PlusToolkit/PlusModelCatalog/fCalPhantom/fCal_1/PhantomDefinition_fCal_1.2_Wiring_1.1.png

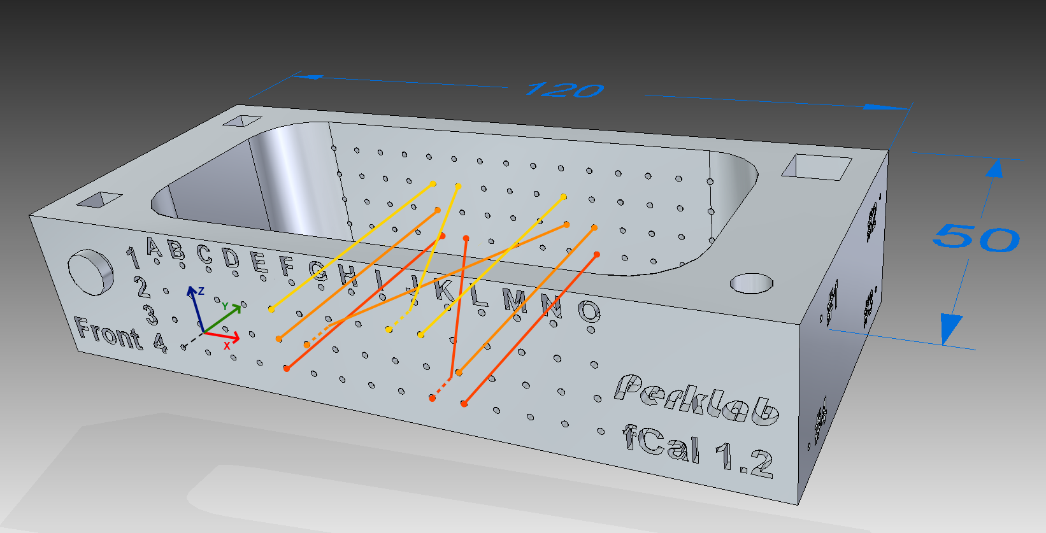
fCalPhantom/fCal_1/PhantomDefinition_fCal_1.2_Wiring_1.1.png
