PlusToolkit/PlusModelCatalog/fCalPhantom/fCal_3/fCal3.1-origin.png

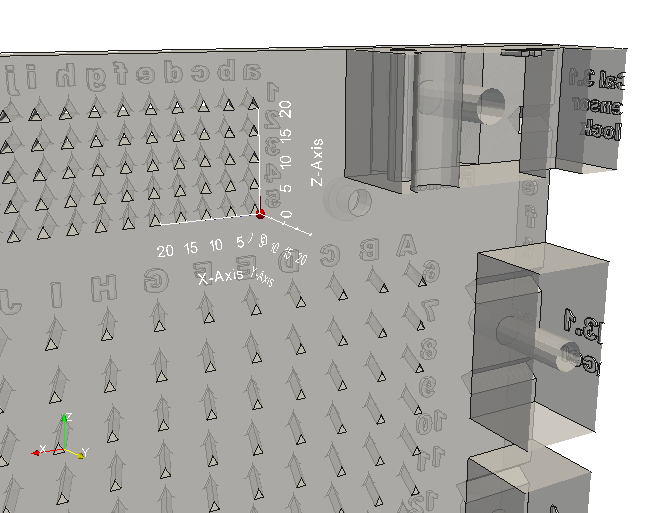
fCalPhantom/fCal_3/fCal3.1-origin.png
