PlusToolkit/PlusModelCatalog/fCalPhantom/fCal_3/fCal3.1.png

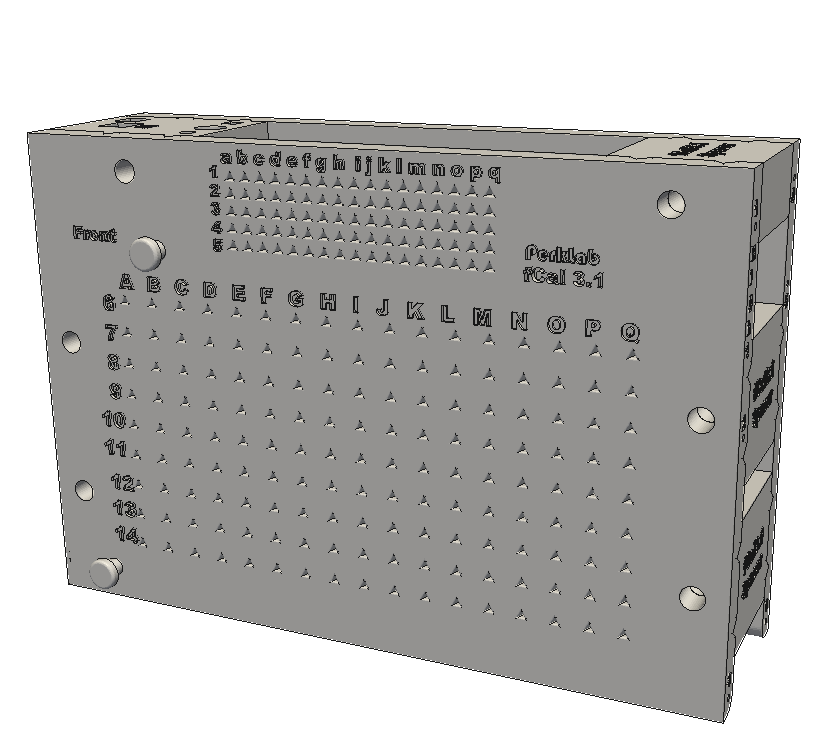
fCalPhantom/fCal_3/fCal3.1.png
