PlusToolkit/PlusModelCatalog/fCalPhantom/fCal_Echo/fCal_Echo1.0.png

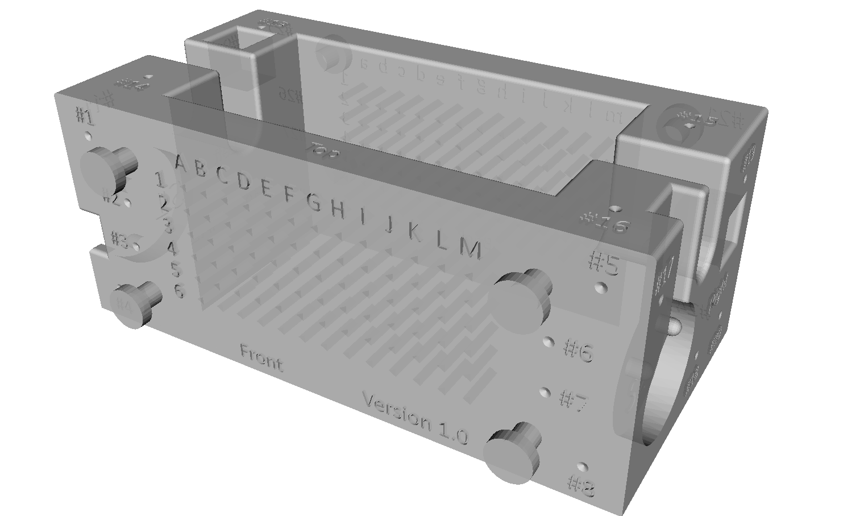
fCalPhantom/fCal_Echo/fCal_Echo1.0.png
