PlusToolkit/PlusModelCatalog/TrackingFixtures/Ascension800Holder_ThreeHolesUp.png

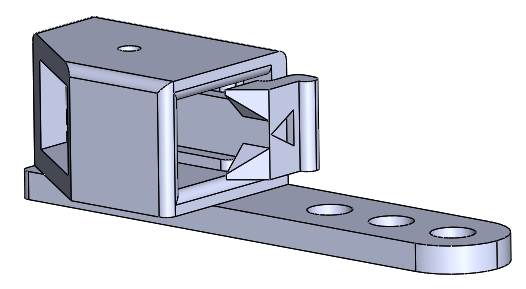
TrackingFixtures/Ascension800Holder_ThreeHolesUp.png
