PlusToolkit/PlusModelCatalog/TrackingFixtures/AscensionStyleAuroraHolder_1.0.PNG

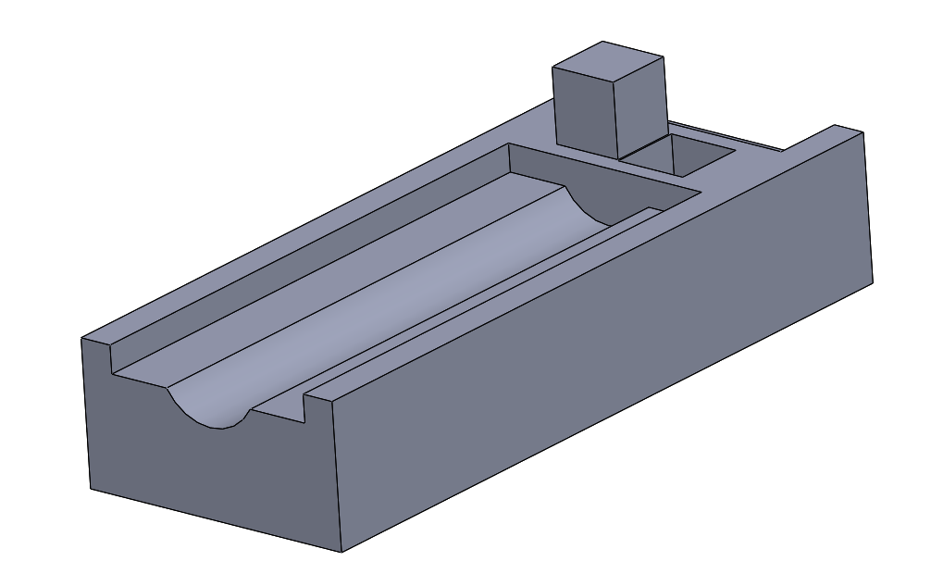
TrackingFixtures/AscensionStyleAuroraHolder_1.0.PNG
