PlusToolkit/PlusModelCatalog/TrackingFixtures/CandyCaneNeedleBase.PNG

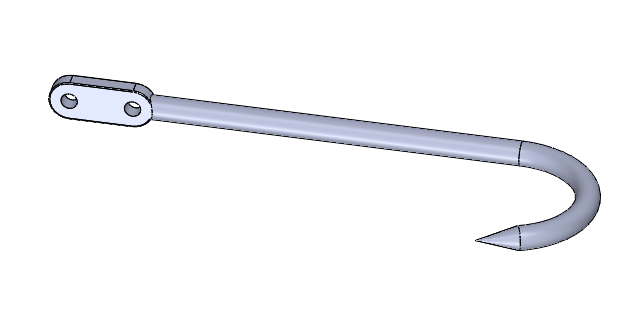
TrackingFixtures/CandyCaneNeedleBase.PNG
