PlusToolkit/PlusModelCatalog/TrackingFixtures/CandyCaneNeedleMarker.PNG

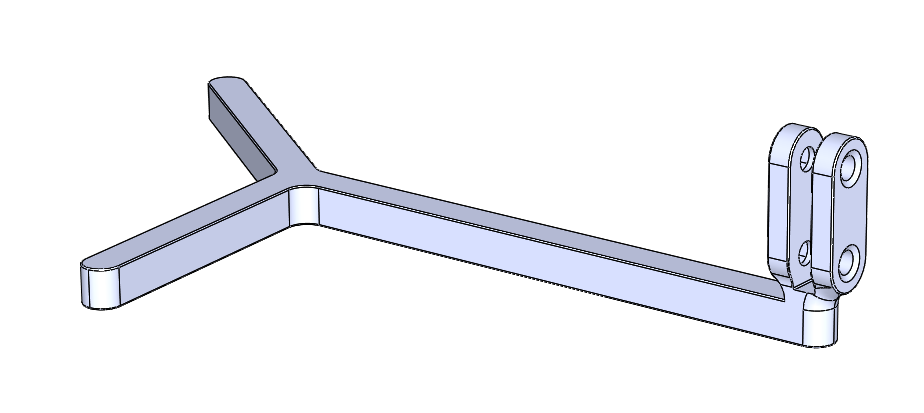
TrackingFixtures/CandyCaneNeedleMarker.PNG
