PlusToolkit/PlusModelCatalog/TrackingFixtures/CauteryGrabber.png

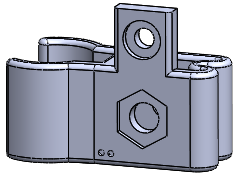
TrackingFixtures/CauteryGrabber.png
