PlusToolkit/PlusModelCatalog/TrackingFixtures/GE_ML6-15-D/GeMl615D_Clip_v01.png

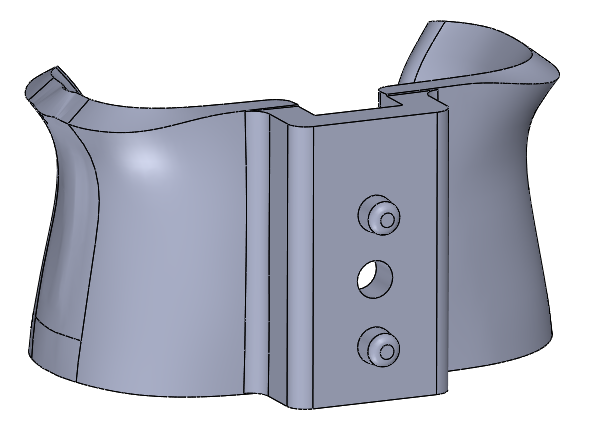
TrackingFixtures/GE_ML6-15-D/GeMl615D_Clip_v01.png
