PlusToolkit/PlusModelCatalog/TrackingFixtures/LureLockMale_SensorHolder.png

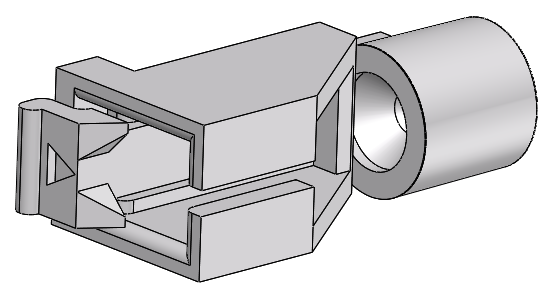
TrackingFixtures/LureLockMale_SensorHolder.png
