PlusToolkit/PlusModelCatalog/TrackingFixtures/NeedleGrabber-BardDuaLok.png

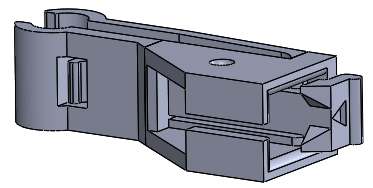
TrackingFixtures/NeedleGrabber-BardDuaLok.png
