PlusToolkit/PlusModelCatalog/TrackingFixtures/OrientationLR-Plane.png

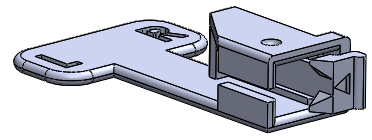
TrackingFixtures/OrientationLR-Plane.png
