PlusToolkit/PlusModelCatalog/TrackingFixtures/SensorHolder-OneHole.png

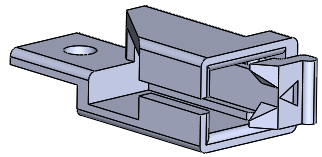
TrackingFixtures/SensorHolder-OneHole.png
