PlusToolkit/PlusModelCatalog/TrackingFixtures/Telemed-MicrUs-L12-SensorHolder.png

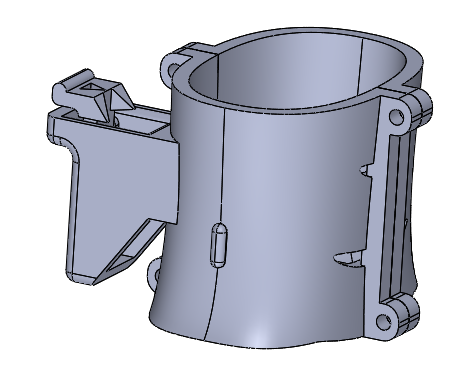
TrackingFixtures/Telemed-MicrUs-L12-SensorHolder.png
