PlusToolkit/PlusModelCatalog/TrackingFixtures/Telemed-MicruUs-C5/Telemed-C5-Brace.png

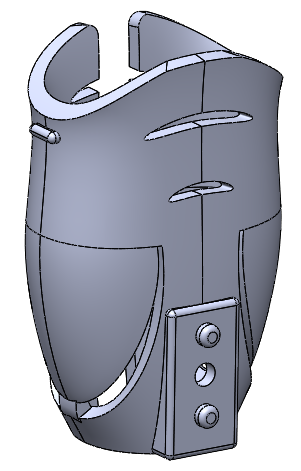
TrackingFixtures/Telemed-MicruUs-C5/Telemed-C5-Brace.png
