PlusToolkit/PlusModelCatalog/TrackingFixtures/Telemed-MicruUs-L12/Telemed-L12-ClipOn.png

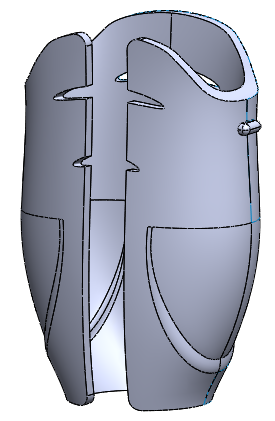
TrackingFixtures/Telemed-MicruUs-L12/Telemed-L12-ClipOn.png
