PlusToolkit/PlusModelCatalog/TrackingFixtures/TelemedHolder-L12_MarkedSide.png

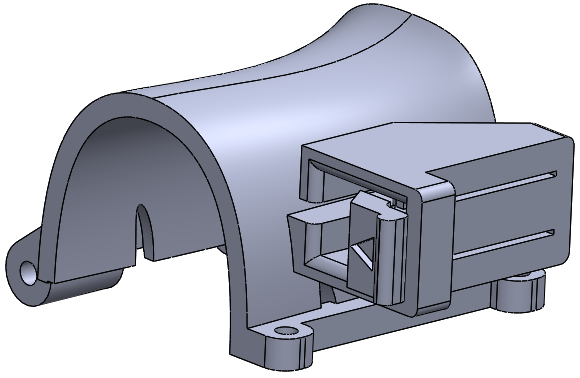
TrackingFixtures/TelemedHolder-L12_MarkedSide.png
