PlusToolkit/PlusModelCatalog/TrackingFixtures/TelemedHolder-L12_UnmarkedSide.png

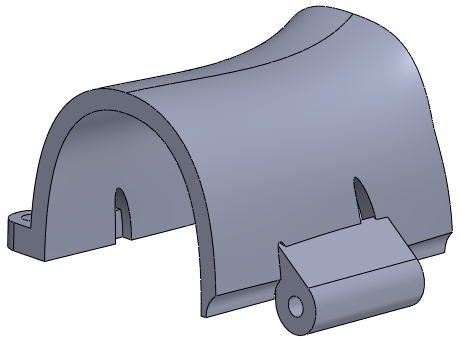
TrackingFixtures/TelemedHolder-L12_UnmarkedSide.png
