PlusToolkit/PlusModelCatalog/fCalPhantom/fCal_L1/BuildingInstructionManual/LPub/parts/3007_14_1275_150_DPCM_1_23_-45.png

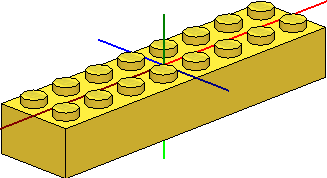
fCalPhantom/fCal_L1/BuildingInstructionManual/LPub/parts/3007_14_1275_150_DPCM_1_23_-45.png
