PlusToolkit/PlusModelCatalog/TrackingFixtures/MC10_ProbeHolder/TelemedMC10_ProbeHolder_MarkedSide.SLDPRT

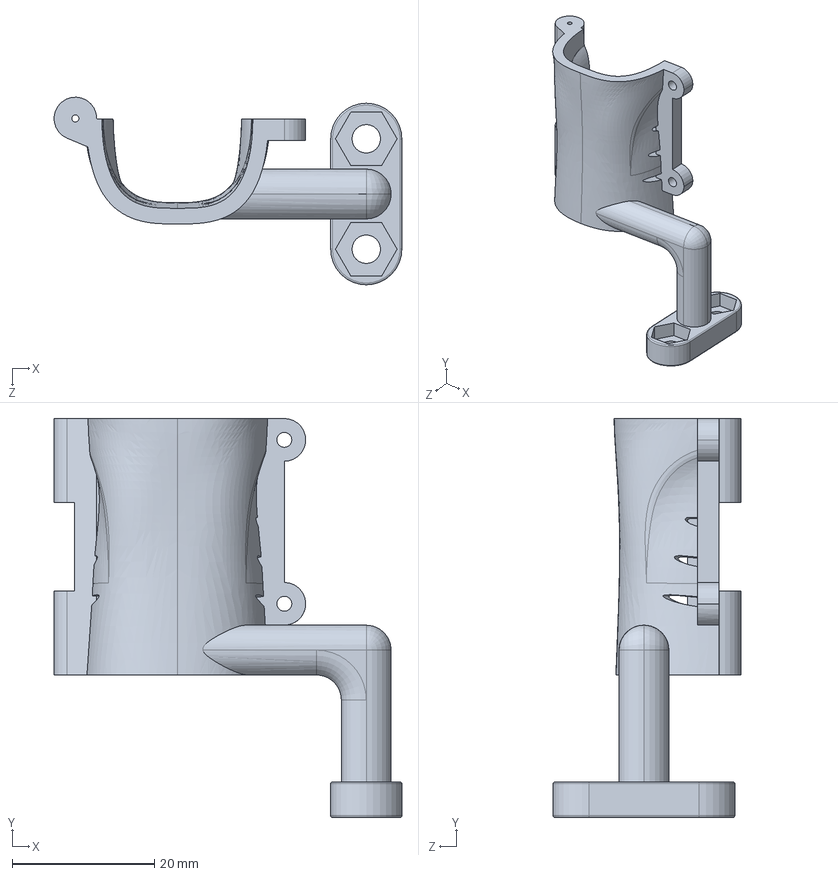
[picture p41: CAD file, 2016-08-29]
TrackingFixtures/MC10_ProbeHolder/TelemedMC10_ProbeHolder_MarkedSide.SLDPRT
48.8 x 56.0 x 26.3 mm
