PlusToolkit/PlusModelCatalog/TrackingFixtures/MicronTracker/MarkerHolder_120mm_Winged_1.0.stl

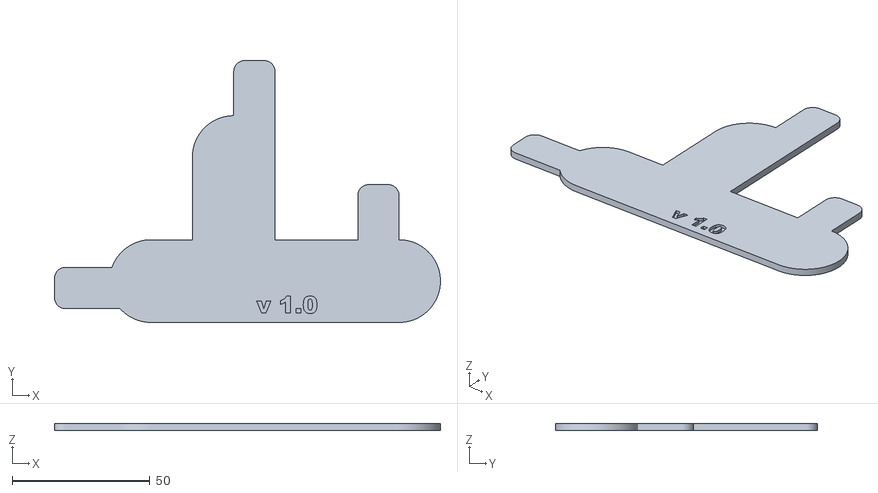
[picture p42: CAD file, 2014-11-28]
TrackingFixtures/MicronTracker/MarkerHolder_120mm_Winged_1.0.stl
140.0 x 95.0 x 2.50
