PlusToolkit/PlusModelCatalog/TrackingFixtures/MultiModalityTracking/SolidWorks/peg1.SLDPRT

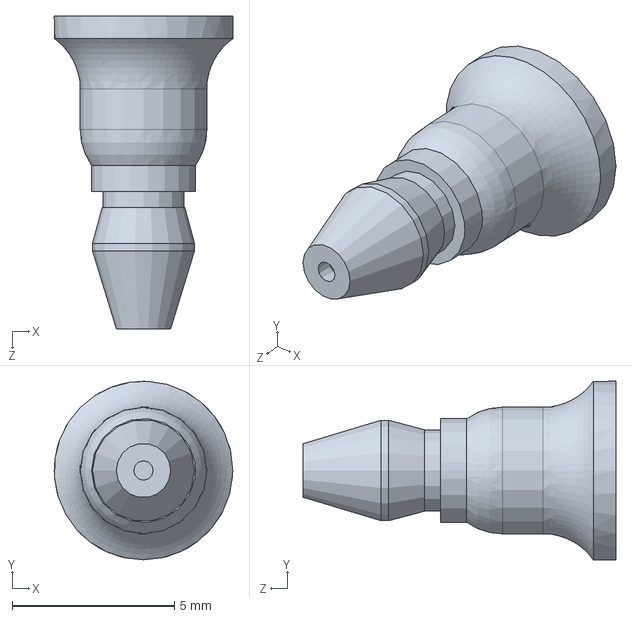
[picture p43: CAD file, 2017-01-05]
TrackingFixtures/MultiModalityTracking/SolidWorks/peg1.SLDPRT
5.50 x 5.50 x 9.64 mm
