PlusToolkit/PlusModelCatalog/TrackingFixtures/OpticalMarkerTracker/Marker-80.SLDPRT

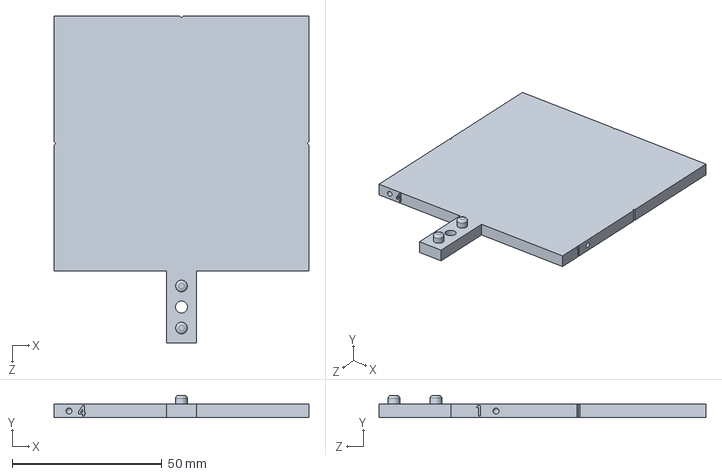
[picture p44: CAD file, 2017-06-23]
TrackingFixtures/OpticalMarkerTracker/Marker-80.SLDPRT
85.0 x 7.50 x 109.0 mm
