PlusToolkit/PlusModelCatalog/TrackingFixtures/OptiTrack/Marker_Ultrasound-OptiTrack.SLDPRT

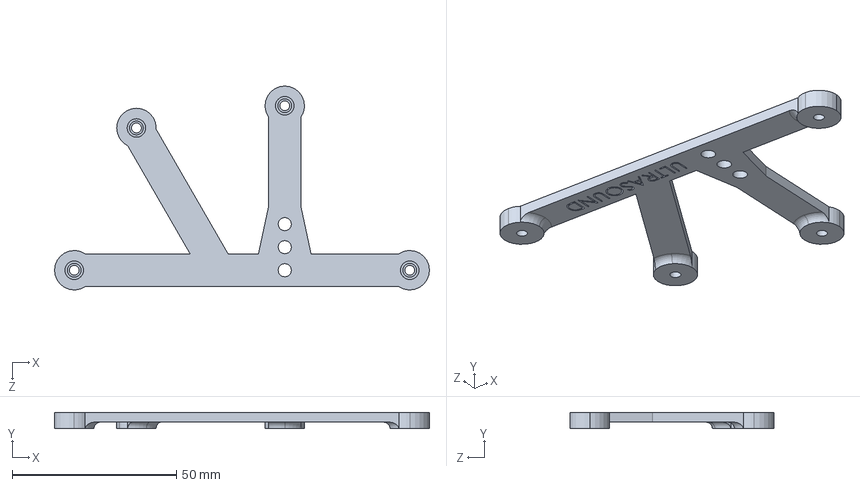
[picture p45: CAD file, 2017-10-10]
TrackingFixtures/OptiTrack/Marker_Ultrasound-OptiTrack.SLDPRT
114.0 x 5.00 x 62.0 mm
