PlusToolkit/PlusModelCatalog/TrackingFixtures/StealthStation/StylusMarker2.SLDPRT

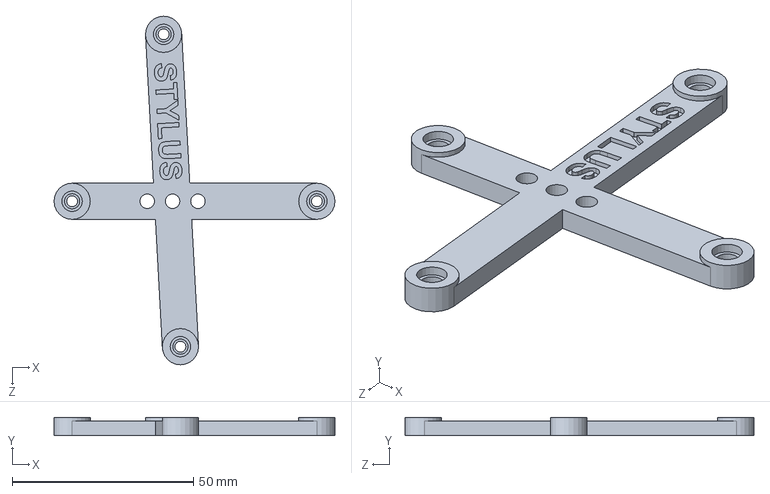
[picture p46: CAD file, 2018-01-19]
TrackingFixtures/StealthStation/StylusMarker2.SLDPRT
77.5 x 5.00 x 96.1 mm
