PlusToolkit/PlusModelCatalog/TrackingFixtures/Telemed-MicruUs-C5/Telemed-C5-Brace.SLDPRT

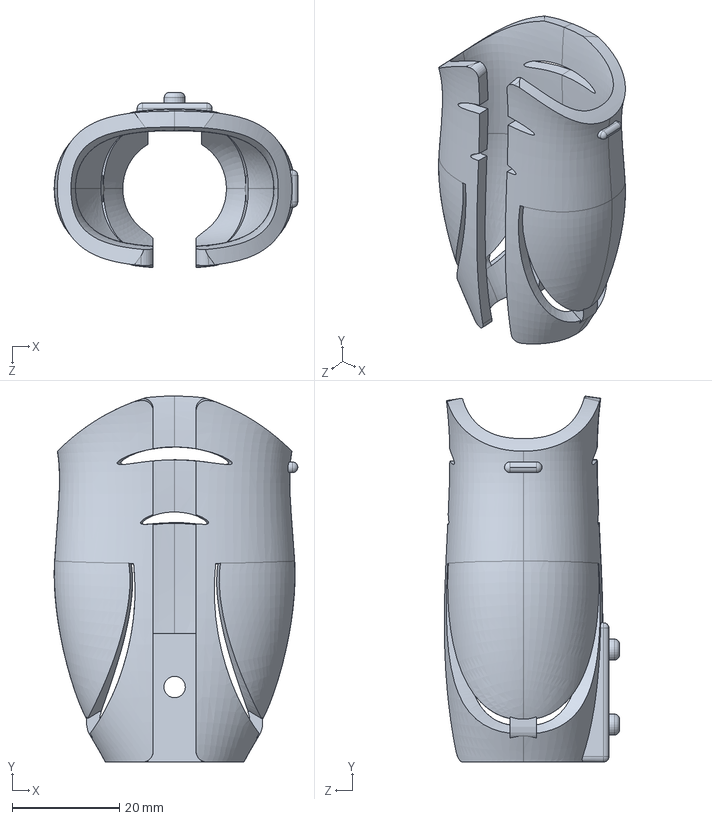
[picture p47: CAD file, 2017-04-27]
TrackingFixtures/Telemed-MicruUs-C5/Telemed-C5-Brace.SLDPRT
45.5 x 68.3 x 32.7 mm
