PlusToolkit/PlusModelCatalog/TrackingFixtures/Telemed-MicruUs-L12/Telemed-L12-ClipOn.SLDPRT

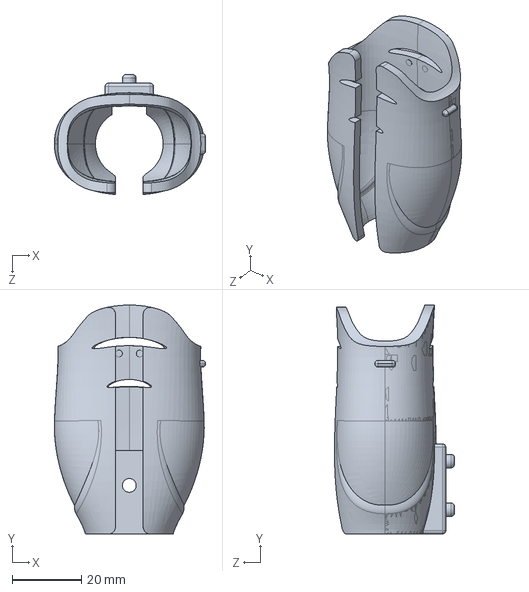
[picture p48: CAD file, 2017-05-24]
TrackingFixtures/Telemed-MicruUs-L12/Telemed-L12-ClipOn.SLDPRT
43.6 x 66.0 x 34.6 mm
