PlusToolkit/PlusModelCatalog/TrackingFixtures/UsCalibrationStylusMarker.stl

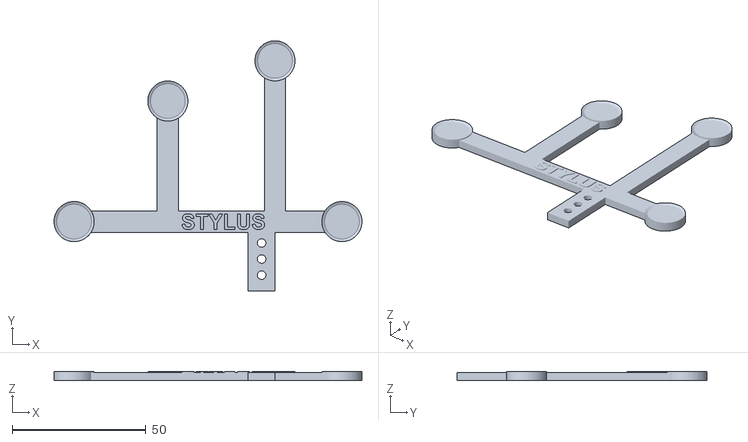
[picture p49: CAD file, 2018-02-23]
TrackingFixtures/UsCalibrationStylusMarker.stl
115.0 x 93.5 x 3.50
