PlusToolkit/PlusModelCatalog/UsNeedleTutor/PhantomFrame.SLDPRT

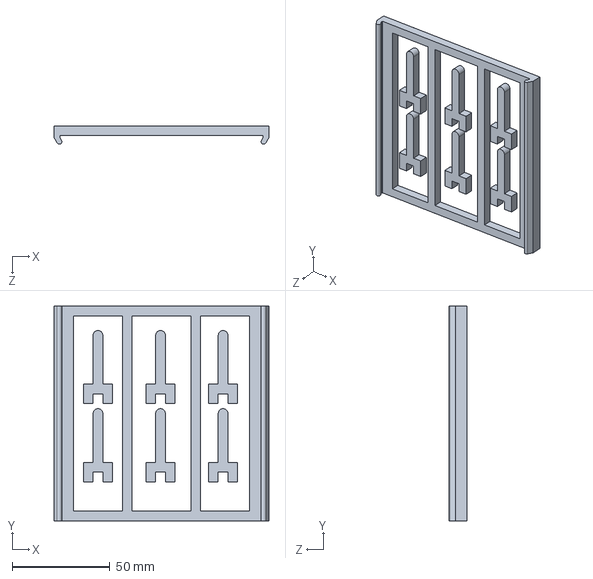
[picture p50: CAD file, 2018-01-30]
UsNeedleTutor/PhantomFrame.SLDPRT
110.0 x 110.0 x 9.45 mm
