PlusToolkit/PlusModelCatalog/fCalPhantom/fCal_3/fCal_3.1_left.stl

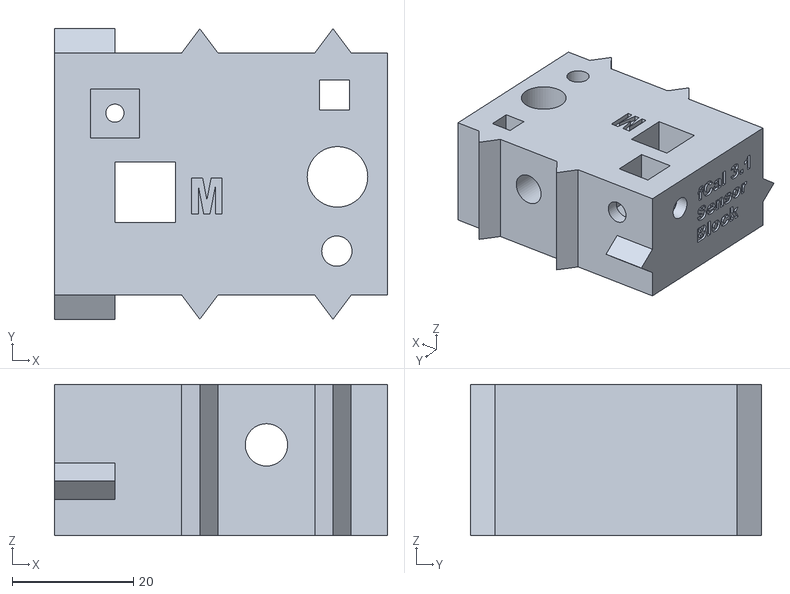
[picture p51: CAD file, 2014-11-28]
fCalPhantom/fCal_3/fCal_3.1_left.stl
55.0 x 48.0 x 25.0
