PlusToolkit/PlusModelCatalog/Tools/Needle_BardDuaLok57.stl

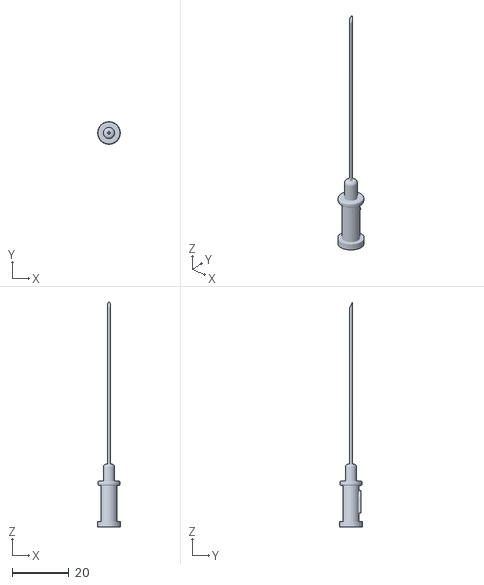
[picture p52: CAD file, 2016-08-08]
Tools/Needle_BardDuaLok57.stl
8.00 x 8.00 x 79.1
