PlusToolkit/PlusModelCatalog/TrackingFixtures/MicronTracker/MarkerHolder_120mm-even_short.stl

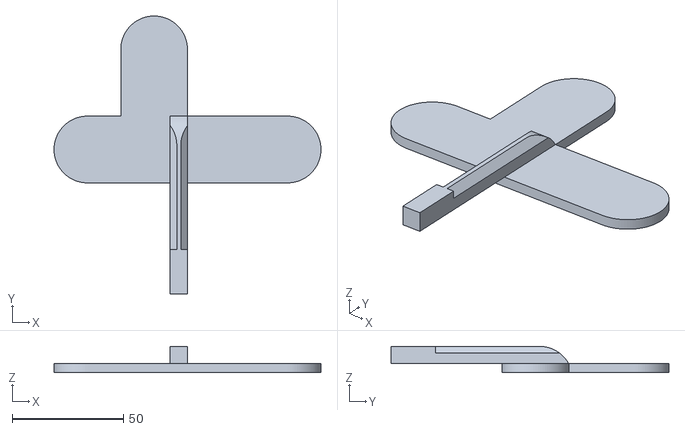
[picture p53: CAD file, 2014-11-28]
TrackingFixtures/MicronTracker/MarkerHolder_120mm-even_short.stl
120.0 x 124.9 x 11.8
