PlusToolkit/PlusModelCatalog/TrackingFixtures/MultiModalityTracking/SolidWorks/SensorHolder_1.0.SLDPRT

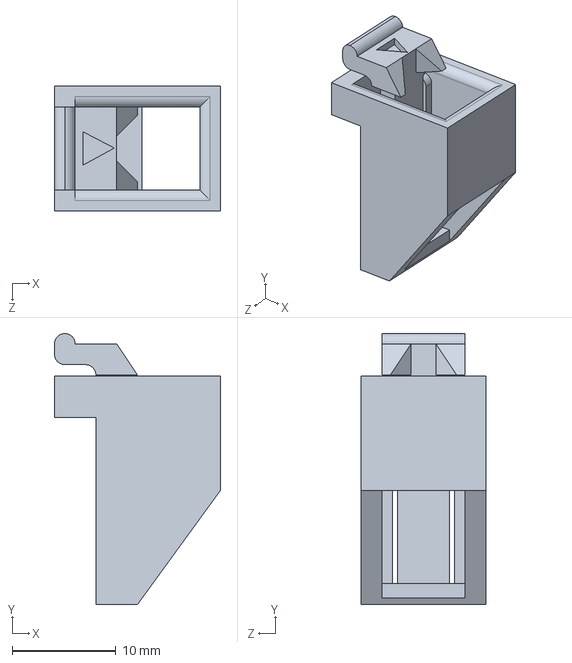
[picture p54: CAD file, 2017-01-05]
TrackingFixtures/MultiModalityTracking/SolidWorks/SensorHolder_1.0.SLDPRT
16.0 x 26.1 x 12.0 mm
