PlusToolkit/PlusModelCatalog/TrackingFixtures/OptiTrack/Marker_Stylus-OptiTrack.SLDPRT

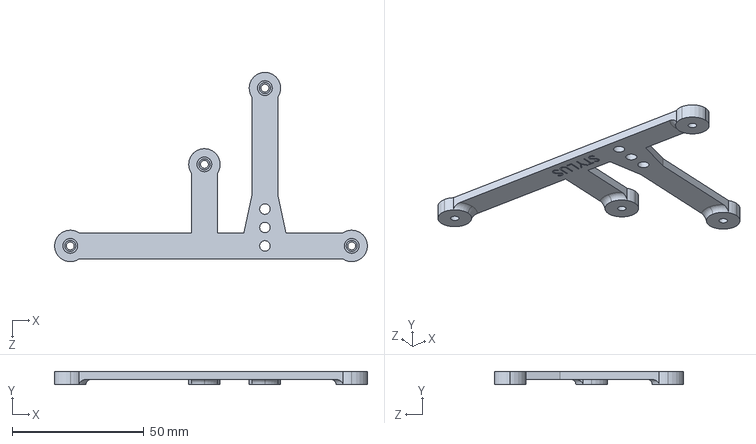
[picture p55: CAD file, 2017-10-10]
TrackingFixtures/OptiTrack/Marker_Stylus-OptiTrack.SLDPRT
119.0 x 5.00 x 72.0 mm
