PlusToolkit/PlusModelCatalog/TrackingFixtures/StealthStation/Stylus_Polaris.SLDPRT

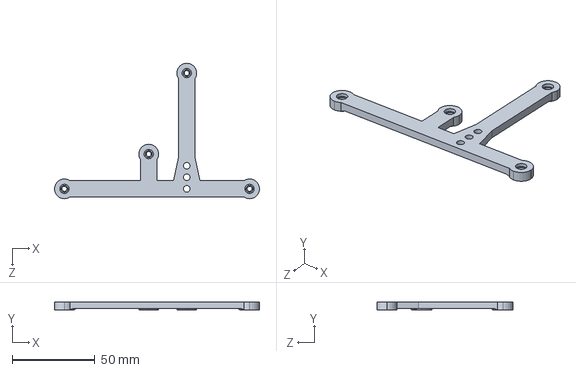
[picture p56: CAD file, 2017-11-28]
TrackingFixtures/StealthStation/Stylus_Polaris.SLDPRT
124.0 x 5.00 x 82.0 mm
