PlusToolkit/PlusModelCatalog/TrackingFixtures/Telemed-MicruUs-C5/Telemed-C5-2R60S.SLDPRT

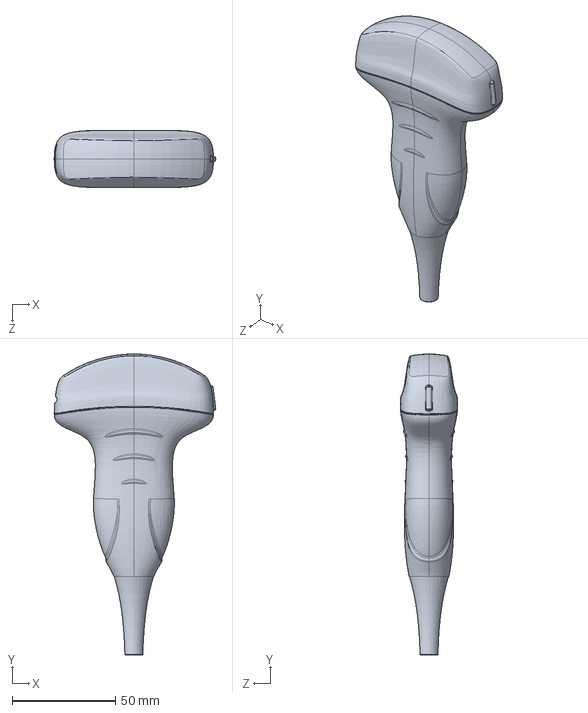
[picture p57: CAD file, 2017-04-27]
TrackingFixtures/Telemed-MicruUs-C5/Telemed-C5-2R60S.SLDPRT
78.1 x 145.5 x 27.7 mm
