PlusToolkit/PlusModelCatalog/TrackingFixtures/UsCalibrationStylus10cm.stl

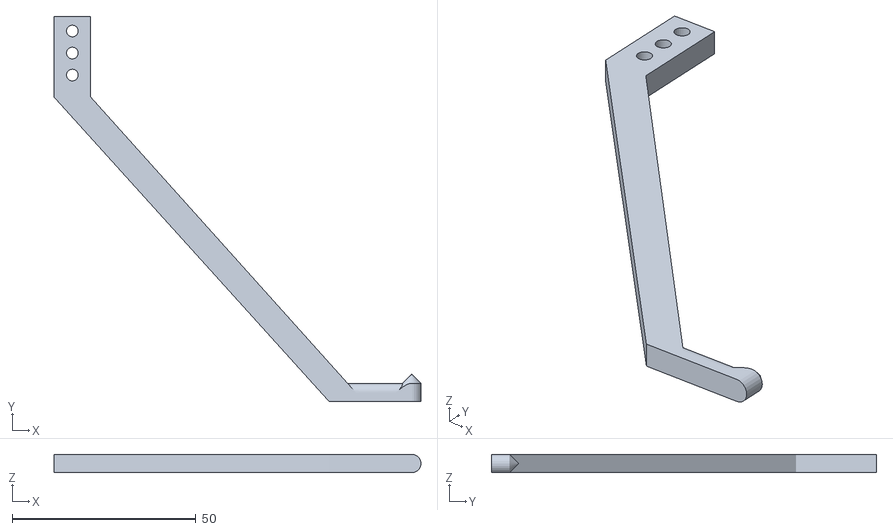
[picture p58: CAD file, 2018-02-23]
TrackingFixtures/UsCalibrationStylus10cm.stl
100.0 x 105.0 x 5.00
