PlusToolkit/PlusModelCatalog/UsNeedleTutor/NeedleMarker.SLDPRT

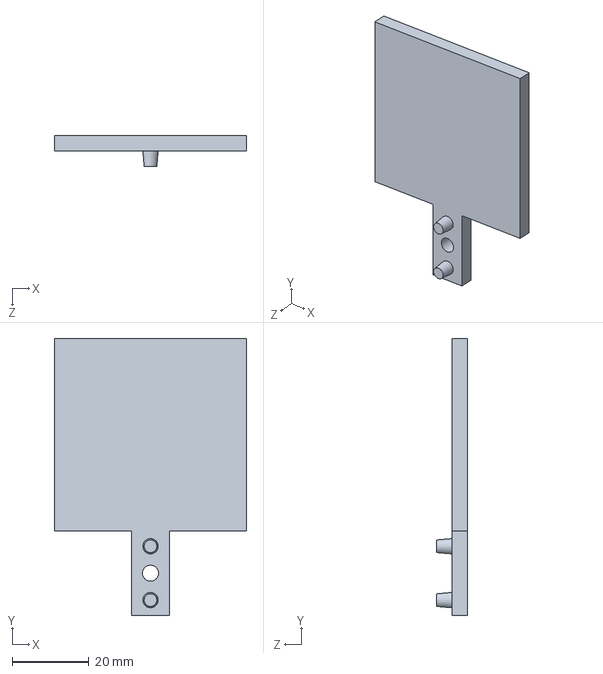
[picture p59: CAD file, 2018-01-30]
UsNeedleTutor/NeedleMarker.SLDPRT
50.0 x 72.0 x 8.00 mm
