PlusToolkit/PlusModelCatalog/fCalPhantom/fCal_3/fCal_3.1_front.stl

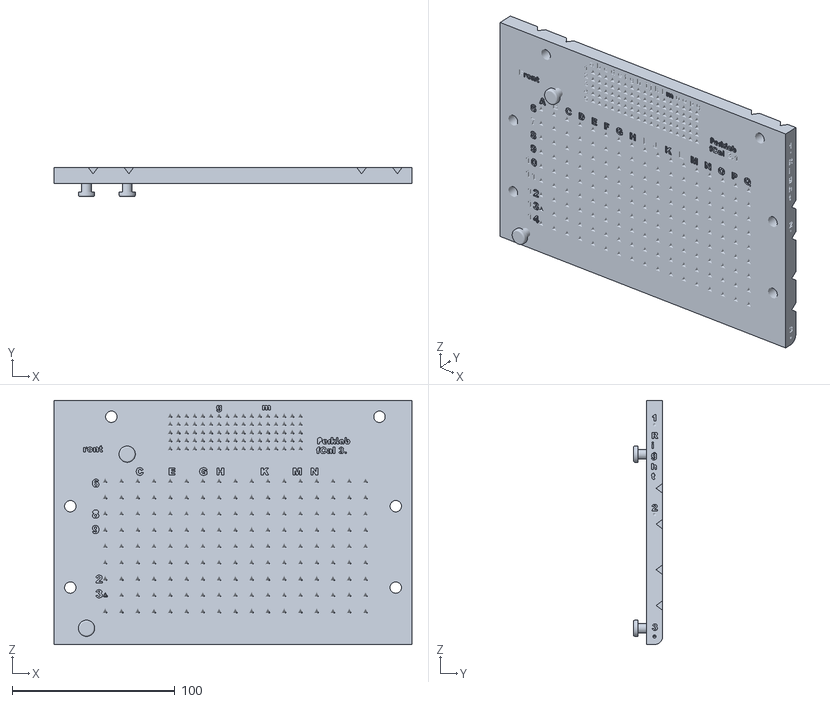
[picture p60: CAD file, 2014-11-28]
fCalPhantom/fCal_3/fCal_3.1_front.stl
220.0 x 18.0 x 150.0
