PlusToolkit/PlusModelCatalog/Tools/UsProbe_Telemed_L12.stl

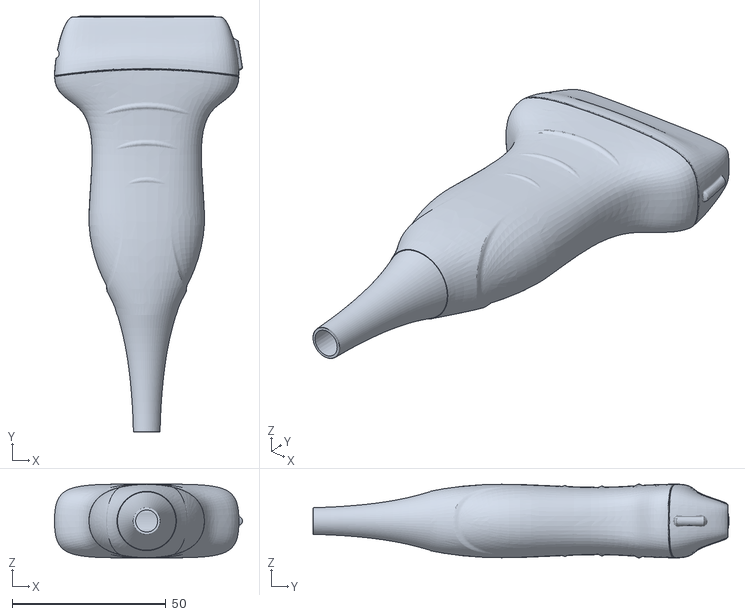
[picture p61: CAD file, 2016-08-08]
Tools/UsProbe_Telemed_L12.stl
61.2 x 135.3 x 24.1
