PlusToolkit/PlusModelCatalog/TrackingFixtures/Block4x4-ThreeHoles.SLDPRT

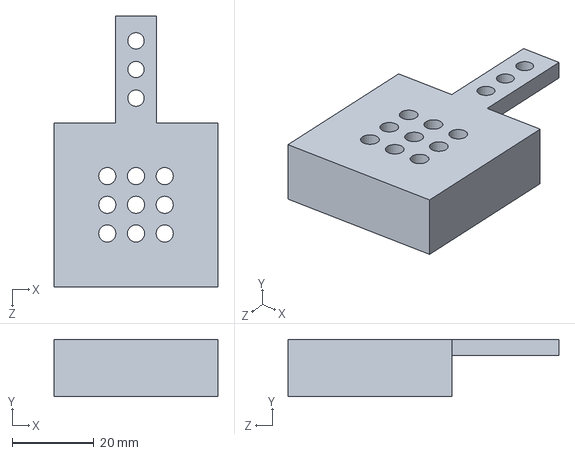
[picture p62: CAD file, 2017-11-28]
TrackingFixtures/Block4x4-ThreeHoles.SLDPRT
40.0 x 14.0 x 66.0 mm
