PlusToolkit/PlusModelCatalog/TrackingFixtures/MC10_ProbeHolder/TelemedMC10_ProbeHolder_UnmarkedSide.SLDPRT

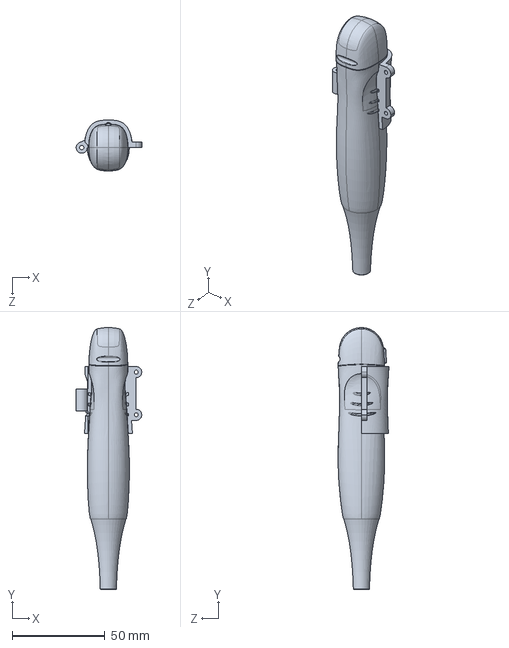
[picture p63: CAD file, 2016-08-05]
TrackingFixtures/MC10_ProbeHolder/TelemedMC10_ProbeHolder_UnmarkedSide.SLDPRT
35.3 x 141.0 x 27.3 mm
