PlusToolkit/PlusModelCatalog/TrackingFixtures/MicronTracker/MarkerHolder_120mm-Short_2.0.stl

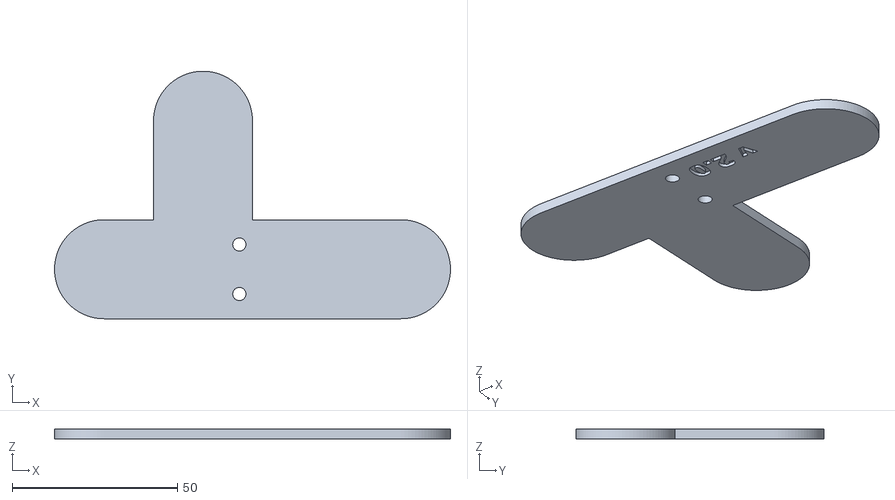
[picture p64: CAD file, 2014-11-28]
TrackingFixtures/MicronTracker/MarkerHolder_120mm-Short_2.0.stl
120.0 x 75.0 x 3.00
