PlusToolkit/PlusModelCatalog/TrackingFixtures/MultiModalityTracking/SolidWorks/PolarisAscensionPlane.SLDPRT

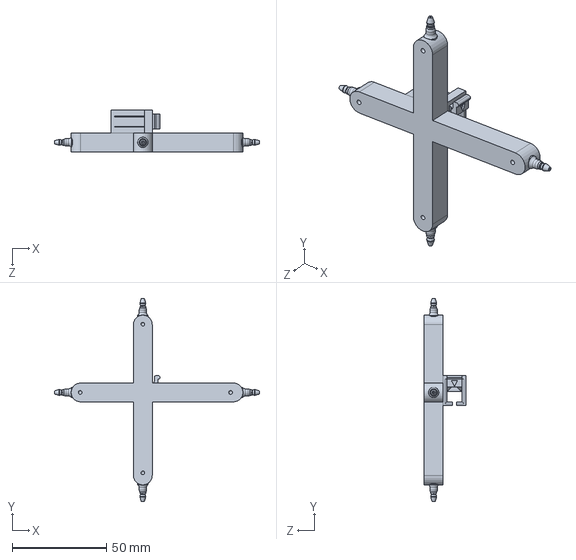
[picture p65: CAD file, 2017-01-05]
TrackingFixtures/MultiModalityTracking/SolidWorks/PolarisAscensionPlane.SLDPRT
108.6 x 107.6 x 22.0 mm
