PlusToolkit/PlusModelCatalog/TrackingFixtures/StealthStation/Ultrasound_Polaris.SLDPRT

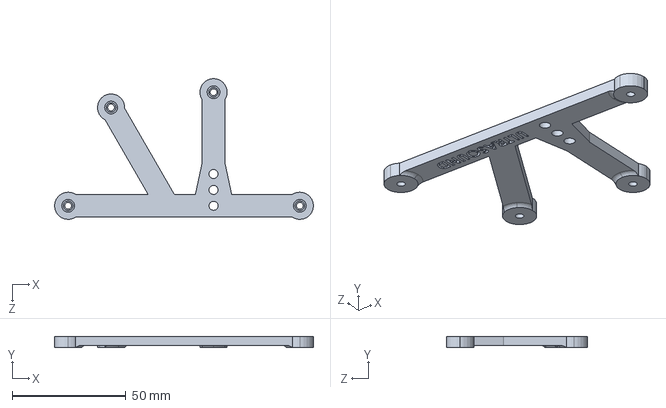
[picture p66: CAD file, 2017-11-28]
TrackingFixtures/StealthStation/Ultrasound_Polaris.SLDPRT
114.0 x 5.00 x 62.0 mm
