PlusToolkit/PlusModelCatalog/UsNeedleTutor/Reference.SLDPRT

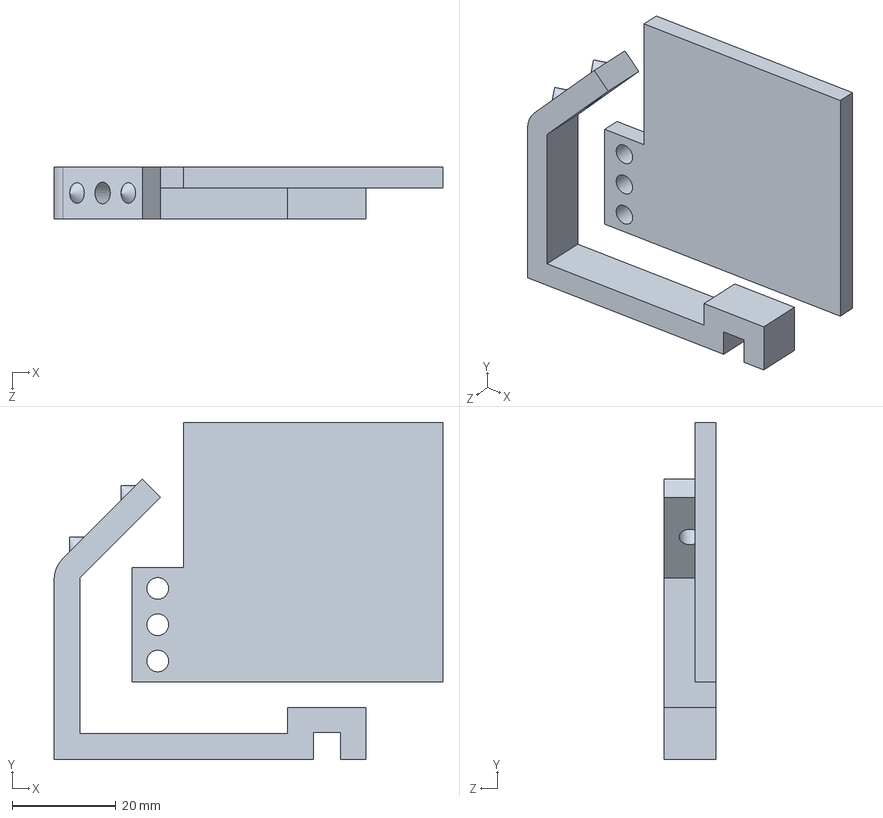
[picture p67: CAD file, 2018-01-30]
UsNeedleTutor/Reference.SLDPRT
75.0 x 65.0 x 10.0 mm
