PlusToolkit/PlusModelCatalog/fCalPhantom/fCal_3/fCal_3.1_spacer.stl

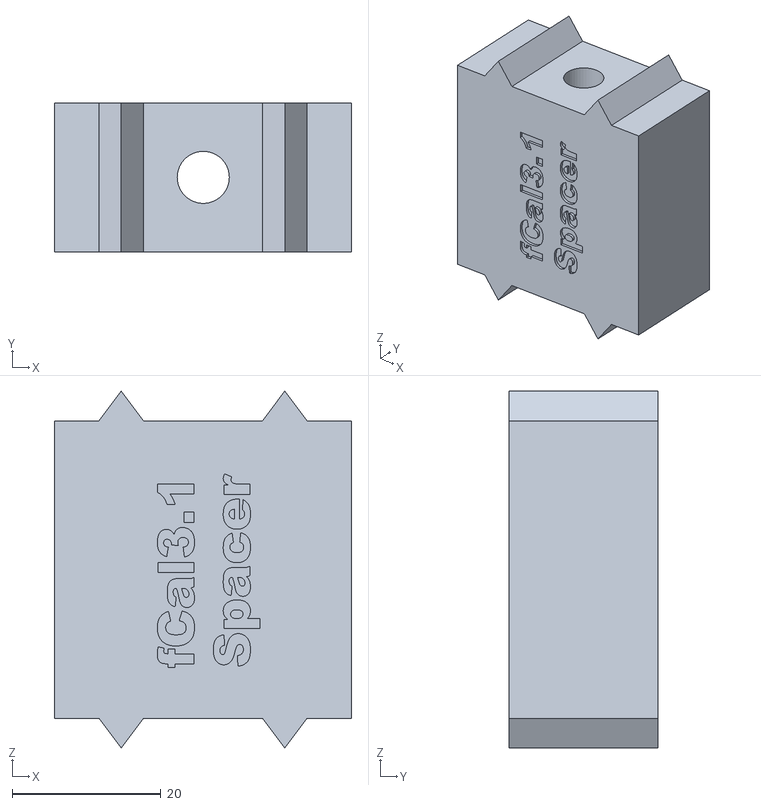
[picture p68: CAD file, 2014-11-28]
fCalPhantom/fCal_3/fCal_3.1_spacer.stl
40.0 x 20.0 x 48.0
