PlusToolkit/PlusModelCatalog/Tools/UsProbe_SPL40.stl

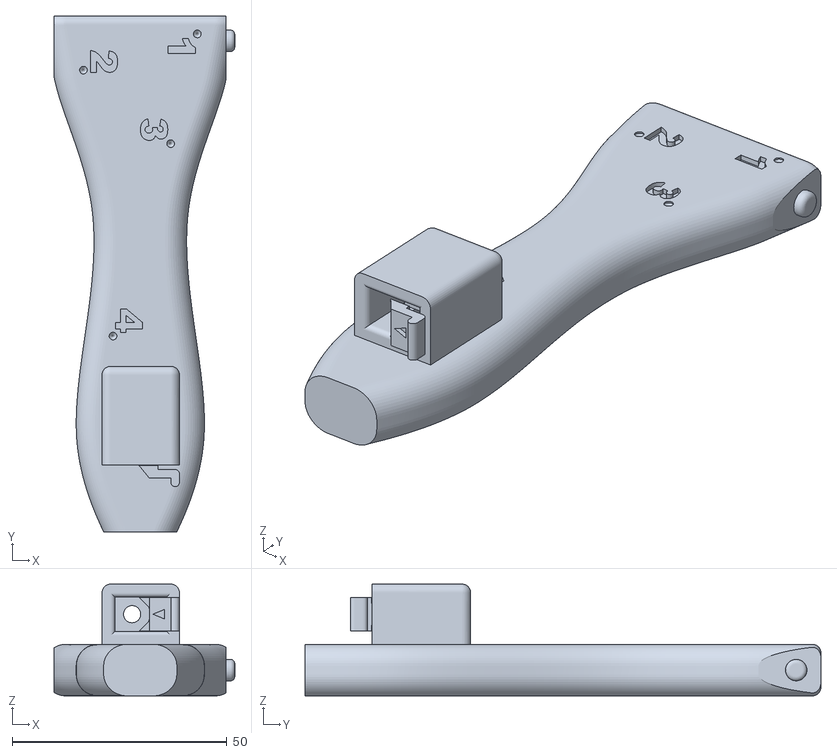
[picture p69: CAD file, 2016-08-05]
Tools/UsProbe_SPL40.stl
42.0 x 120.0 x 26.0
