PlusToolkit/PlusModelCatalog/TrackingFixtures/ArmL-30.STL

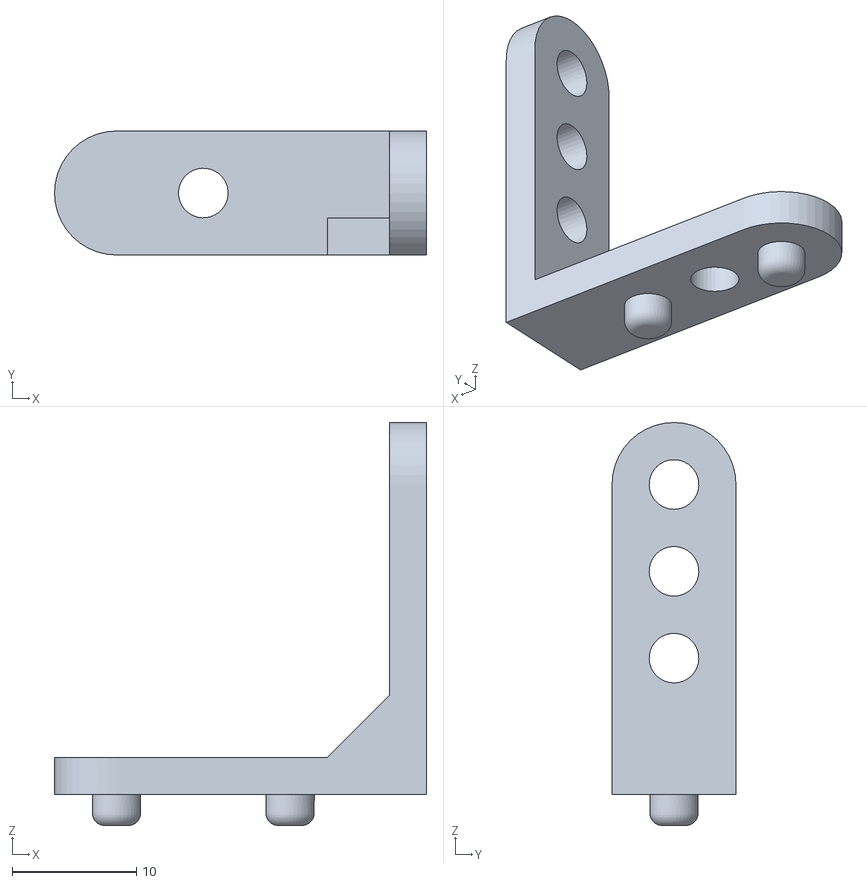
[picture p70: CAD file, 2017-11-28]
TrackingFixtures/ArmL-30.STL
30.0 x 10.0 x 32.5
