PlusToolkit/PlusModelCatalog/TrackingFixtures/MC10_ProbeHolder/TelemedMC10_ProbeHolder_OpticalTracker.SLDPRT

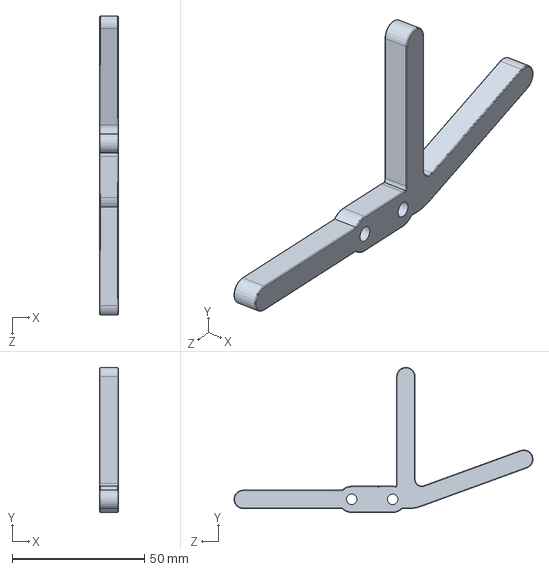
[picture p71: CAD file, 2016-08-05]
TrackingFixtures/MC10_ProbeHolder/TelemedMC10_ProbeHolder_OpticalTracker.SLDPRT
7.00 x 54.9 x 113.1 mm
