PlusToolkit/PlusModelCatalog/TrackingFixtures/MicronTracker/MarkerHolder_120mm-even_long.stl

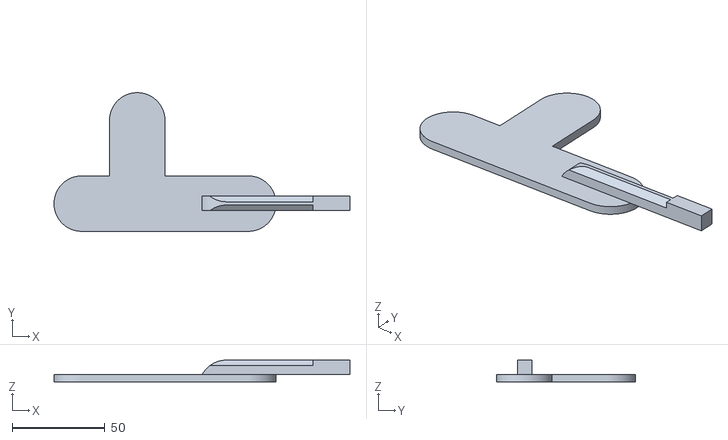
[picture p72: CAD file, 2014-11-28]
TrackingFixtures/MicronTracker/MarkerHolder_120mm-even_long.stl
160.0 x 75.0 x 11.8
