PlusToolkit/PlusModelCatalog/TrackingFixtures/StealthStation/Marker_Peg-Insert-OptiTrack.SLDPRT

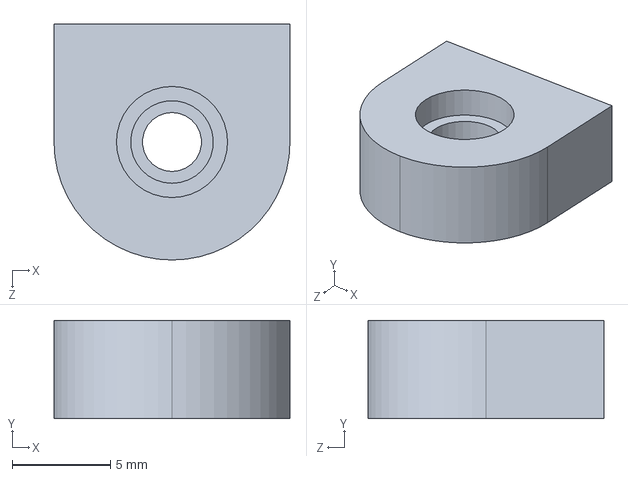
[picture p73: CAD file, 2017-11-28]
TrackingFixtures/StealthStation/Marker_Peg-Insert-OptiTrack.SLDPRT
12.0 x 5.00 x 12.0 mm
