PlusToolkit/PlusModelCatalog/UsNeedleTutor/UltrasoundLinear.SLDPRT

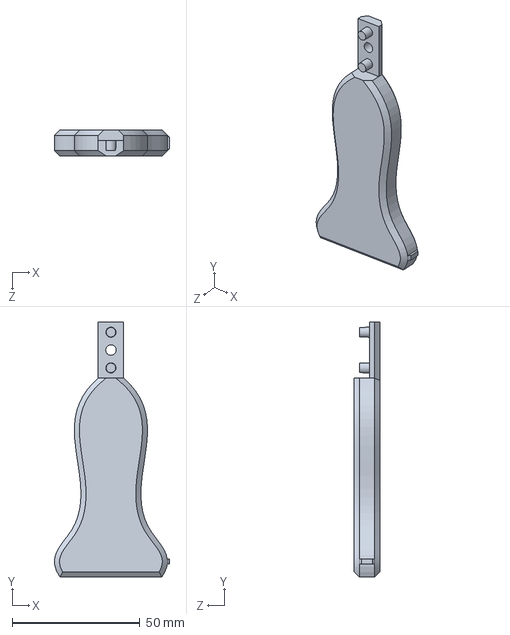
[picture p74: CAD file, 2018-01-30]
UsNeedleTutor/UltrasoundLinear.SLDPRT
45.2 x 100.0 x 10.0 mm
