PlusToolkit/PlusModelCatalog/fCalPhantom/fCal_3/fCal_3.1_back.stl

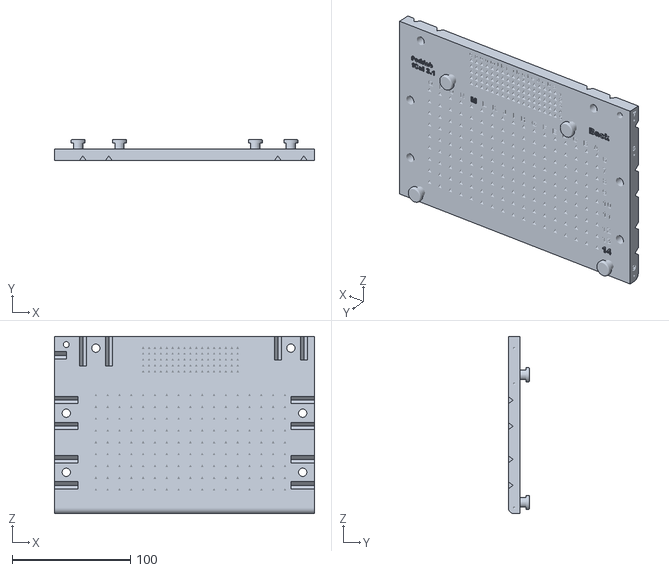
[picture p75: CAD file, 2014-11-28]
fCalPhantom/fCal_3/fCal_3.1_back.stl
220.0 x 18.0 x 150.0
