PlusToolkit/PlusModelCatalog/Tools/UsProbe_Ultrasonix_L14-5_38.stl

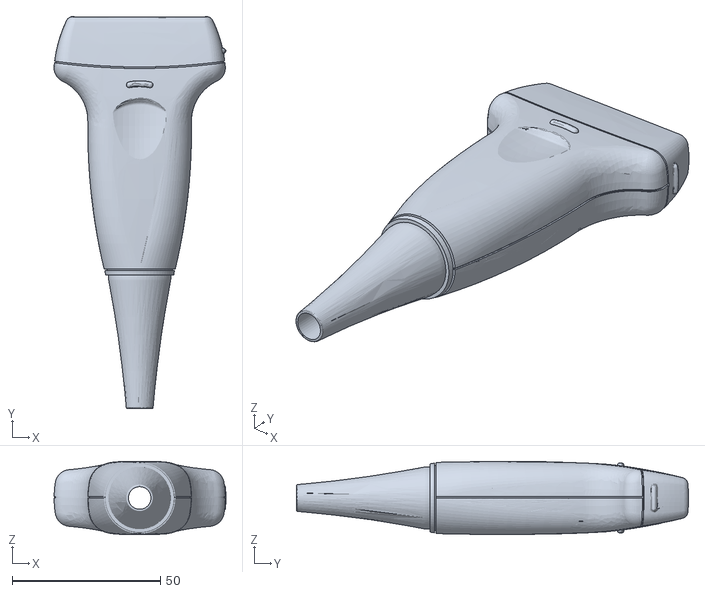
[picture p76: CAD file, 2016-08-05]
Tools/UsProbe_Ultrasonix_L14-5_38.stl
57.9 x 132.0 x 24.6
