PlusToolkit/PlusModelCatalog/TrackingFixtures/CandyCaneNeedleMarker.SLDPRT

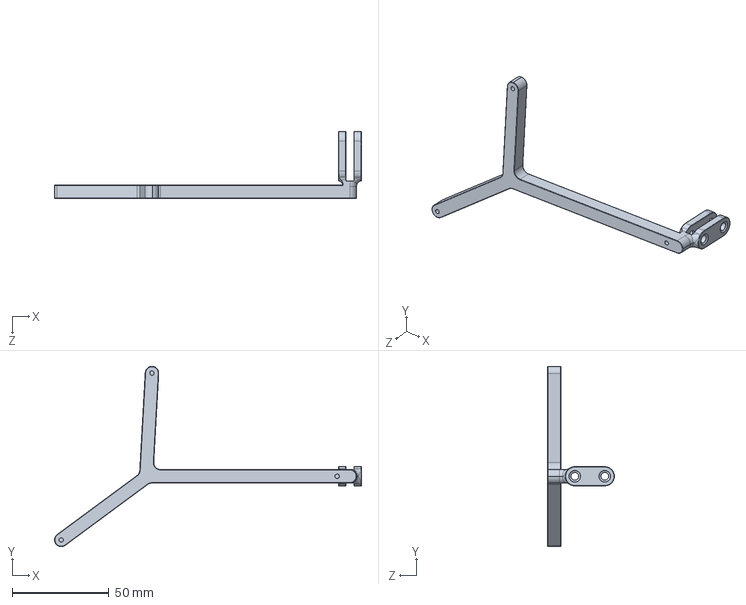
[picture p77: CAD file, 2017-06-01]
TrackingFixtures/CandyCaneNeedleMarker.SLDPRT
158.8 x 93.3 x 34.6 mm
