PlusToolkit/PlusModelCatalog/TrackingFixtures/StealthStation/Reference.SLDPRT

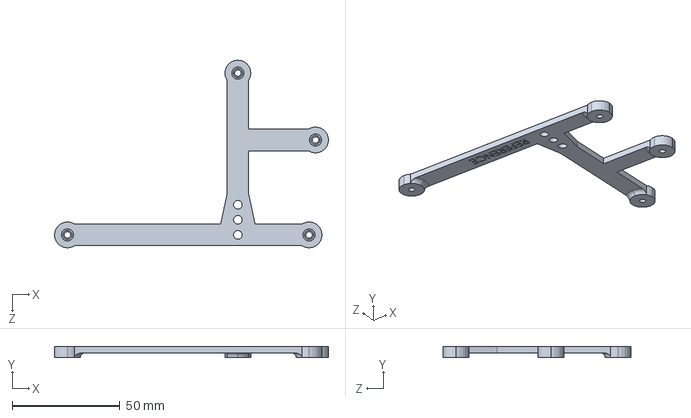
[picture p78: CAD file, 2017-11-28]
TrackingFixtures/StealthStation/Reference.SLDPRT
127.0 x 5.00 x 87.0 mm
