PlusToolkit/PlusModelCatalog/UsNeedleTutor/LuerMale.SLDPRT

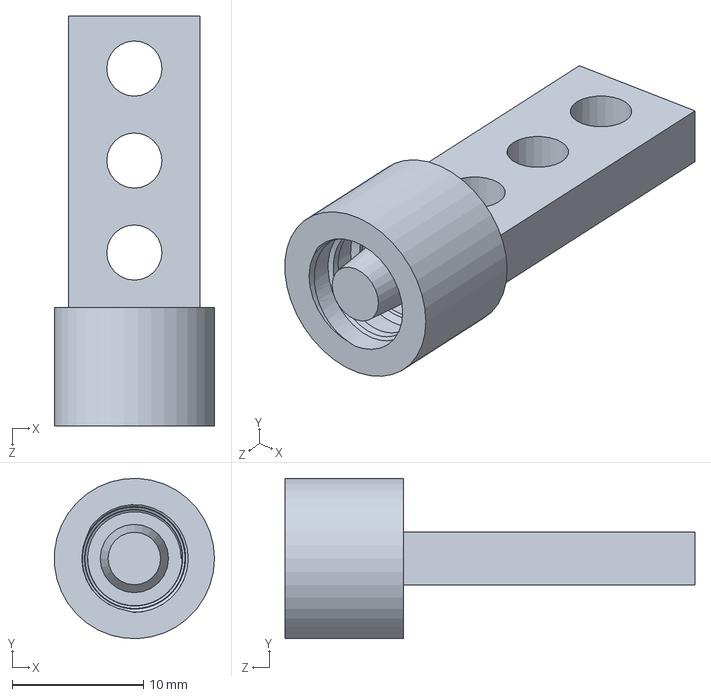
[picture p79: CAD file, 2018-01-30]
UsNeedleTutor/LuerMale.SLDPRT
12.2 x 12.2 x 31.2 mm
