PlusToolkit/PlusModelCatalog/Tools/UsProbe_Ultrasonix_C5-2_60.stl

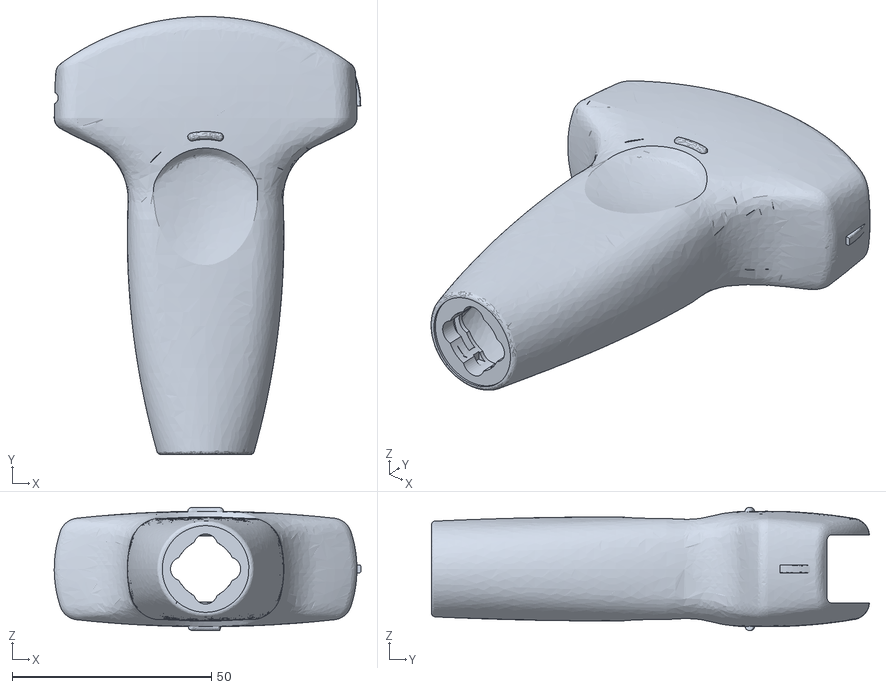
[picture p80: CAD file, 2016-08-05]
Tools/UsProbe_Ultrasonix_C5-2_60.stl
77.0 x 110.0 x 30.9
