PlusToolkit/PlusModelCatalog/TrackingFixtures/CandyCaneNeedleBase.SLDPRT

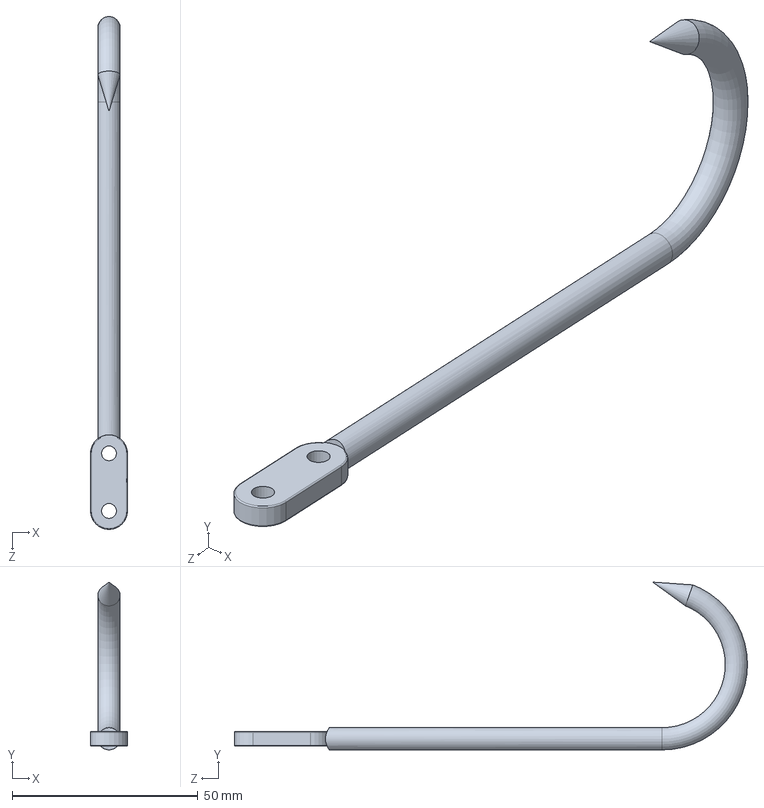
[picture p81: CAD file, 2017-06-01]
TrackingFixtures/CandyCaneNeedleBase.SLDPRT
10.0 x 45.2 x 138.2 mm
