PlusToolkit/PlusModelCatalog/UsNeedleTutor/UltrasoundMarker.SLDPRT

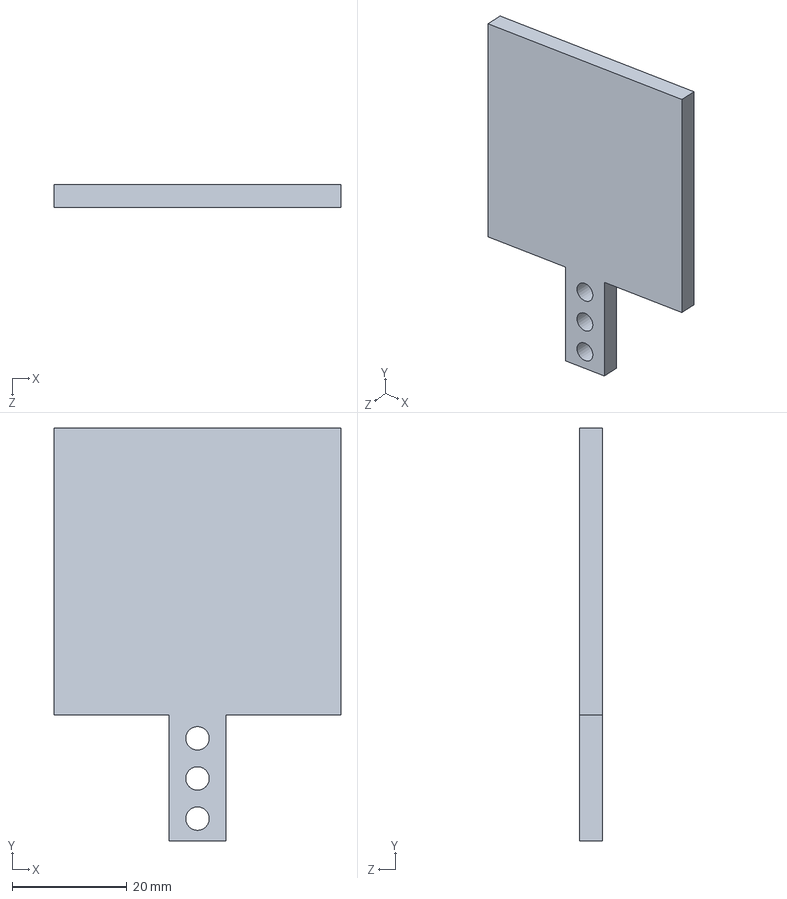
[picture p82: CAD file, 2018-01-30]
UsNeedleTutor/UltrasoundMarker.SLDPRT
50.0 x 72.0 x 4.00 mm
