PlusToolkit/PlusModelCatalog/Tools/UsProbe_Ultrasonix_EC9-5_10.stl

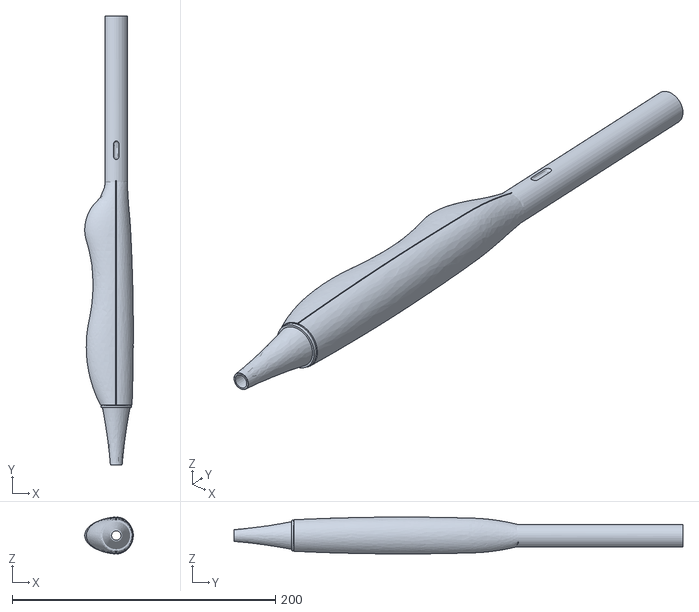
[picture p83: CAD file, 2016-08-05]
Tools/UsProbe_Ultrasonix_EC9-5_10.stl
37.0 x 341.0 x 28.0
