PlusToolkit/PlusModelCatalog/TrackingFixtures/SensorHolder_1.0.SLDPRT

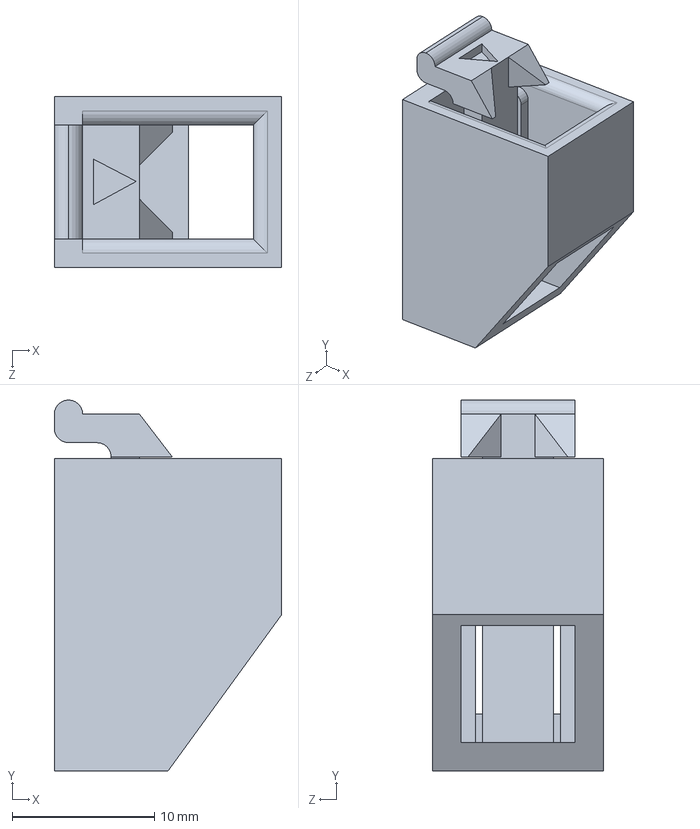
[picture p84: CAD file, 2017-05-24]
TrackingFixtures/SensorHolder_1.0.SLDPRT
16.0 x 26.1 x 12.0 mm
