PlusToolkit/PlusModelCatalog/Tools/Cautery.SLDPRT

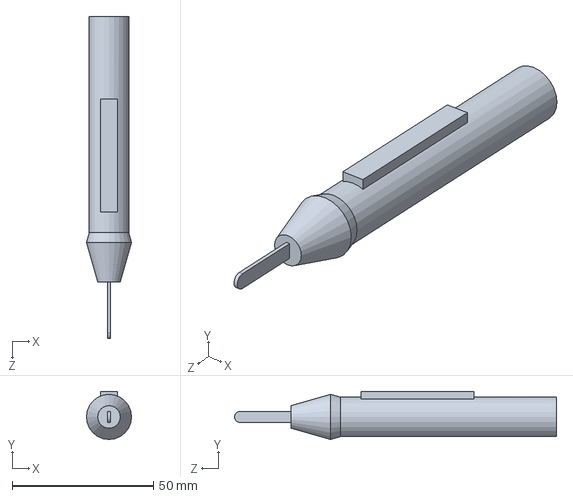
[picture p85: CAD file, 2016-04-06]
Tools/Cautery.SLDPRT
16.0 x 17.0 x 114.0 mm
