PlusToolkit/PlusModelCatalog/TrackingFixtures/Ascension800Holder_ThreeHolesSide.SLDPRT

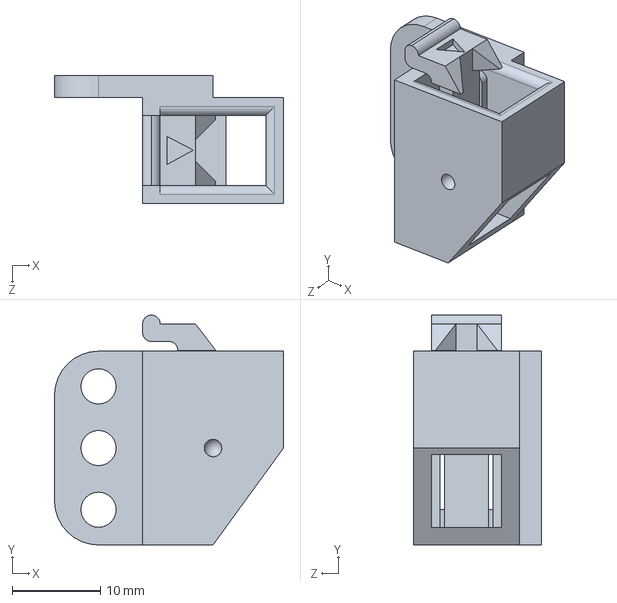
[picture p86: CAD file, 2017-05-24]
TrackingFixtures/Ascension800Holder_ThreeHolesSide.SLDPRT
26.0 x 26.1 x 14.5 mm
