PlusToolkit/PlusModelCatalog/TrackingFixtures/Medtronic_PN9733157_Marker.SLDPRT

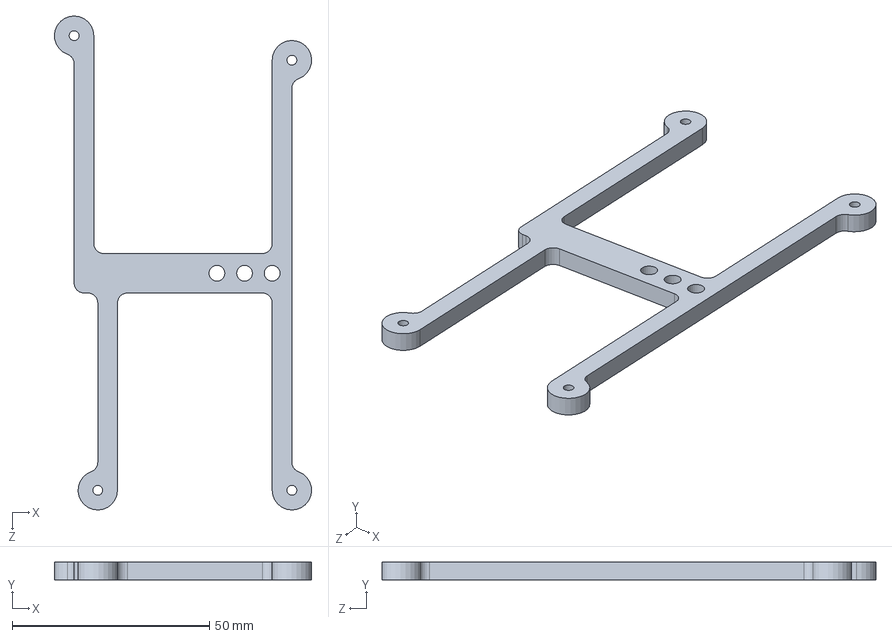
[picture p87: CAD file, 2017-05-24]
TrackingFixtures/Medtronic_PN9733157_Marker.SLDPRT
65.2 x 4.50 x 125.2 mm
