PlusToolkit/PlusModelCatalog/TrackingFixtures/Ascension800Holder_ThreeHolesUp.SLDPRT

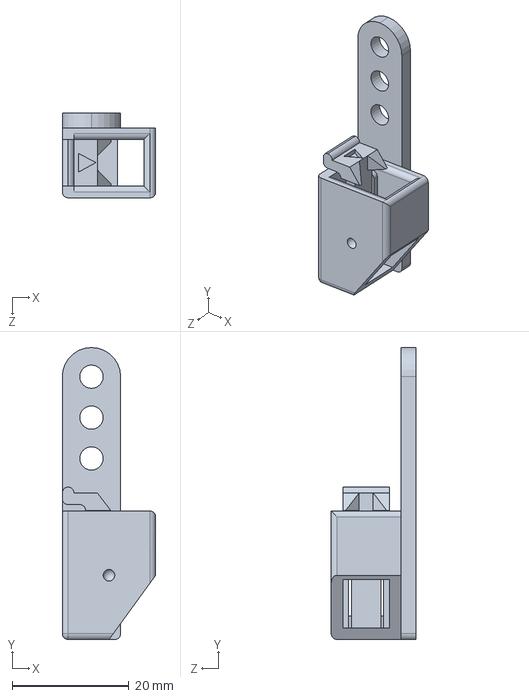
[picture p88: CAD file, 2017-05-16]
TrackingFixtures/Ascension800Holder_ThreeHolesUp.SLDPRT
16.0 x 50.0 x 14.5 mm
