PlusToolkit/PlusModelCatalog/TrackingFixtures/PolarisMarker1.SLDPRT

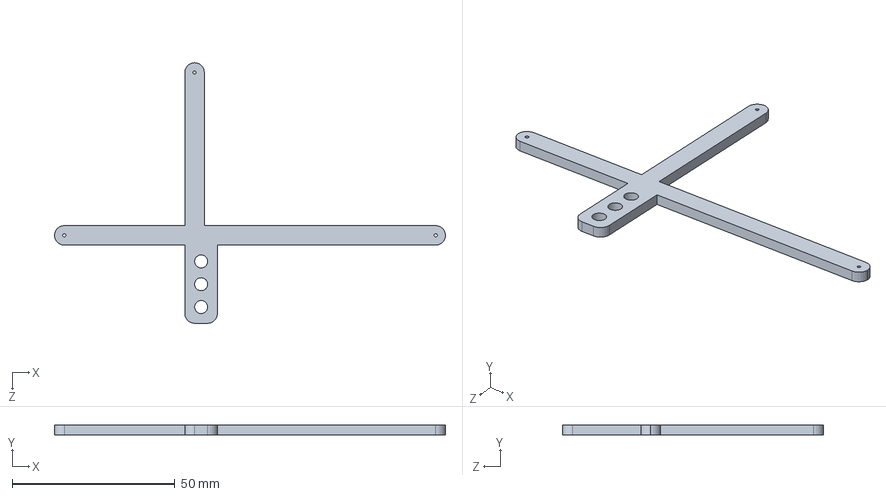
[picture p89: CAD file, 2017-02-26]
TrackingFixtures/PolarisMarker1.SLDPRT
120.0 x 3.00 x 80.0 mm
