PlusToolkit/PlusModelCatalog/TrackingFixtures/TelemedHolder_L12_MarkedSide.SLDPRT

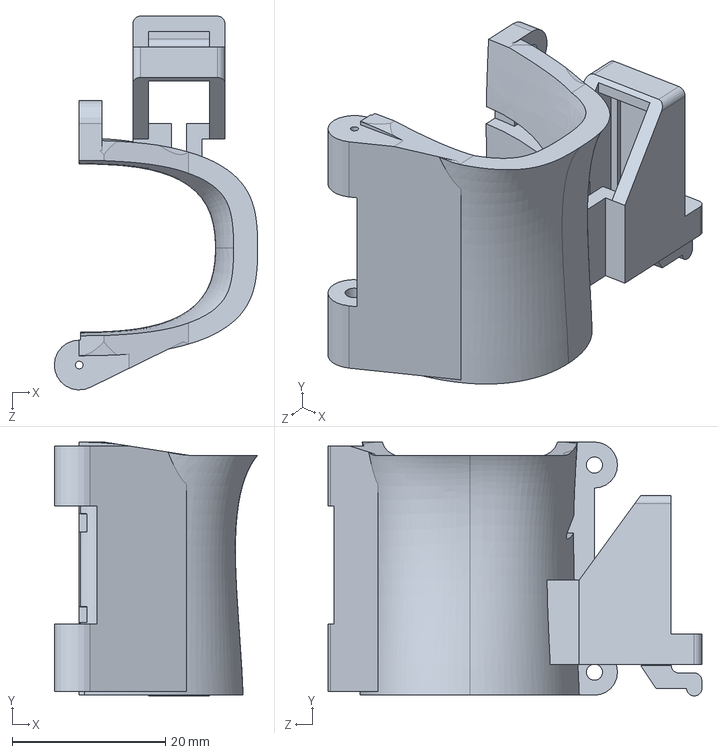
[picture p90: CAD file, 2017-01-19]
TrackingFixtures/TelemedHolder_L12_MarkedSide.SLDPRT
26.5 x 33.1 x 48.7 mm
