PlusToolkit/PlusModelCatalog/TrackingFixtures/TelemedHolder-L12_UnmarkedSide.sldprt

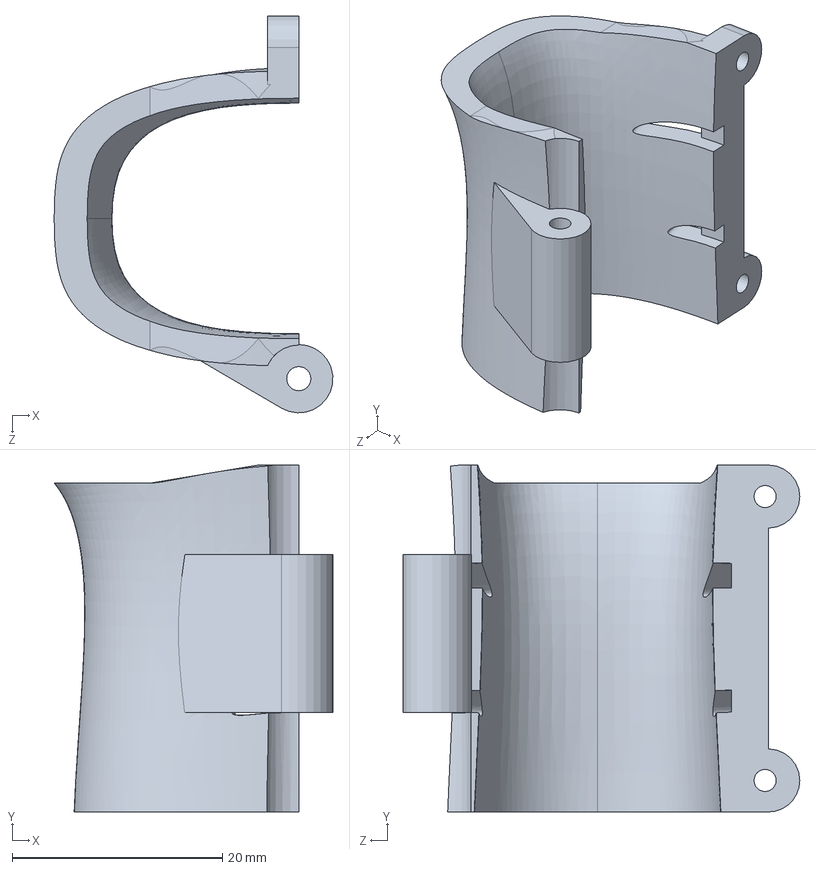
[picture p91: CAD file, 2017-01-19]
TrackingFixtures/TelemedHolder-L12_UnmarkedSide.sldprt
26.5 x 33.0 x 37.7 mm
