PlusToolkit/PlusModelCatalog/TrackingFixtures/Stylus_100mm.stl

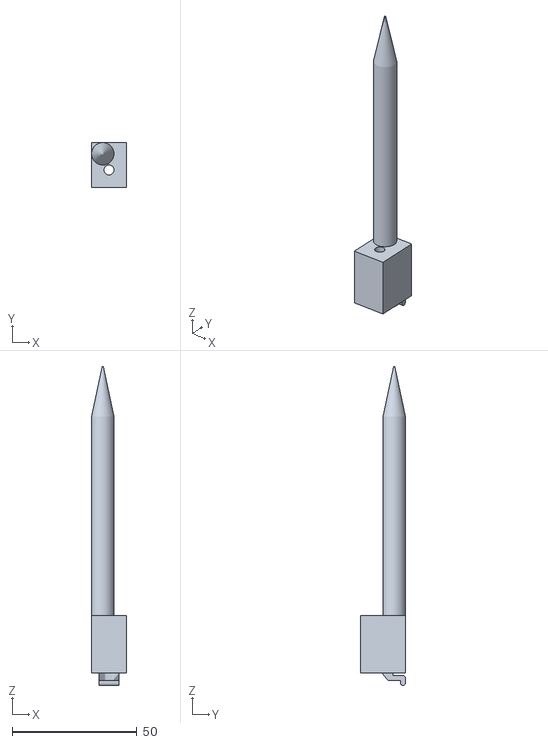
[picture p92: CAD file, 2016-12-06]
TrackingFixtures/Stylus_100mm.stl
14.0 x 18.0 x 128.0
