PlusToolkit/PlusModelCatalog/TrackingFixtures/Stylus_Candycane_70mm_1.0.stl

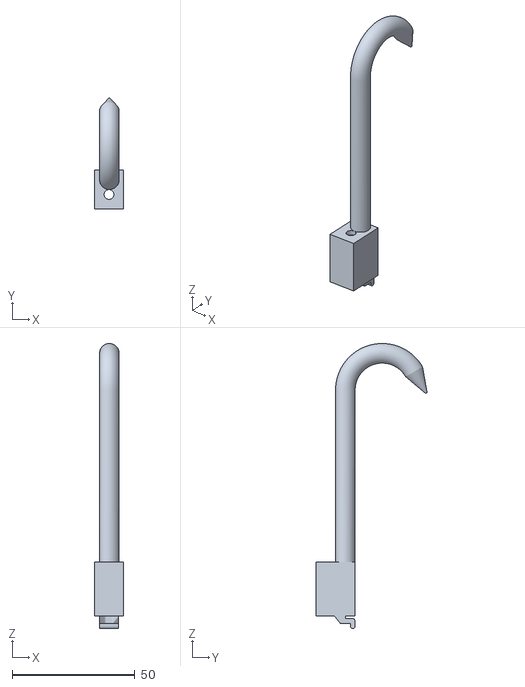
[picture p93: CAD file, 2016-12-06]
TrackingFixtures/Stylus_Candycane_70mm_1.0.stl
12.0 x 45.3 x 116.1
