PlusToolkit/PlusModelCatalog/TrackingFixtures/AscensionStyleAuroraHolder_1.0.SLDPRT

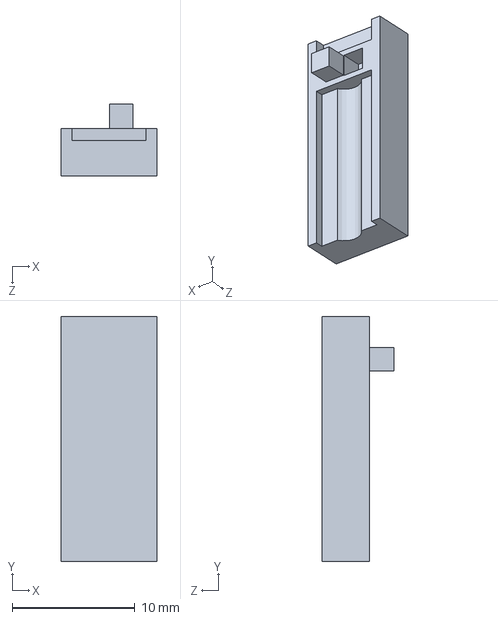
[picture p94: CAD file, 2016-12-05]
TrackingFixtures/AscensionStyleAuroraHolder_1.0.SLDPRT
7.80 x 20.0 x 5.90 mm
