PlusToolkit/PlusModelCatalog/TrackingFixtures/LureLockMale_SensorHolder.SLDPRT

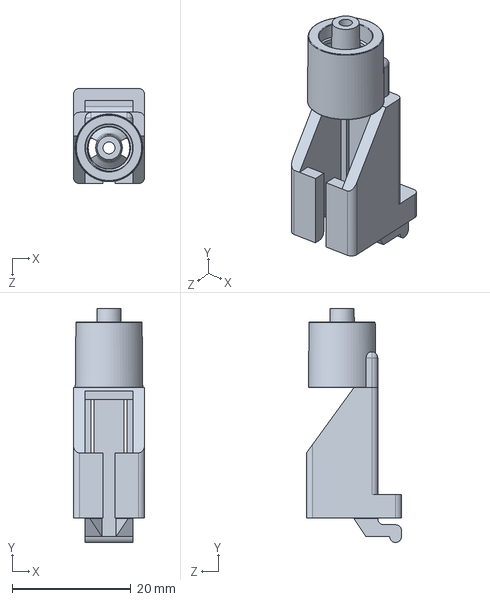
[picture p95: CAD file, 2016-11-18]
TrackingFixtures/LureLockMale_SensorHolder.SLDPRT
12.0 x 39.4 x 16.0 mm
