PlusToolkit/PlusModelCatalog/TrackingFixtures/LureLockMale.SLDPRT

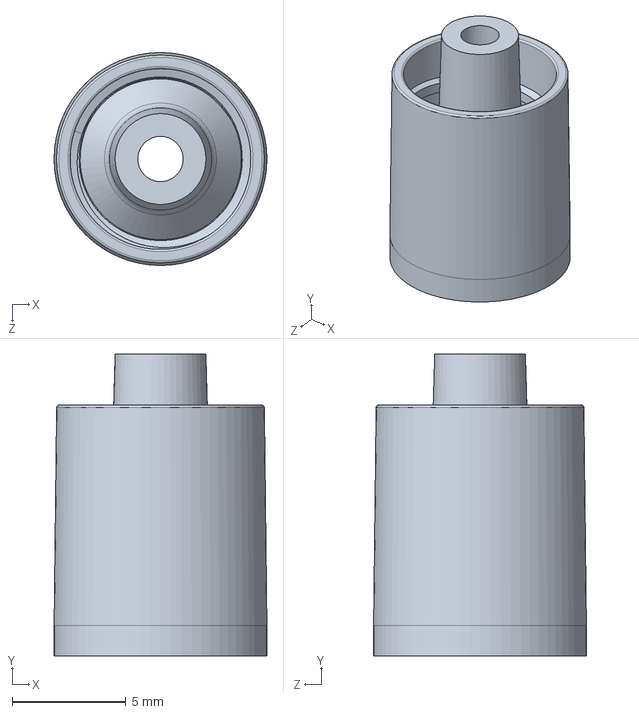
[picture p96: CAD file, 2016-11-10]
TrackingFixtures/LureLockMale.SLDPRT
9.38 x 13.3 x 9.38 mm
