PlusToolkit/PlusModelCatalog/TrackingFixtures/NeedleGrabber_Parallel_Short.SLDPRT

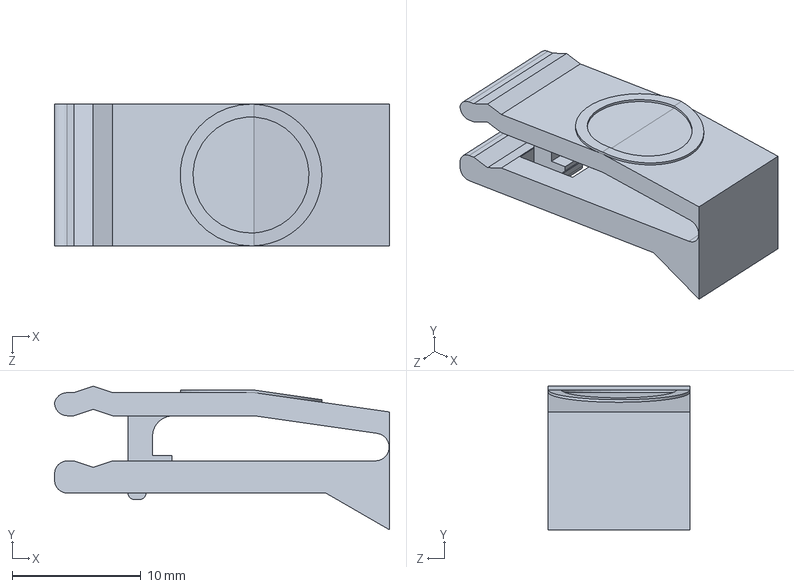
[picture p97: CAD file, 2016-08-17]
TrackingFixtures/NeedleGrabber_Parallel_Short.SLDPRT
26.0 x 11.2 x 11.0 mm
