PlusToolkit/PlusModelCatalog/TrackingFixtures/Micron_Maker04-White.SLDPRT

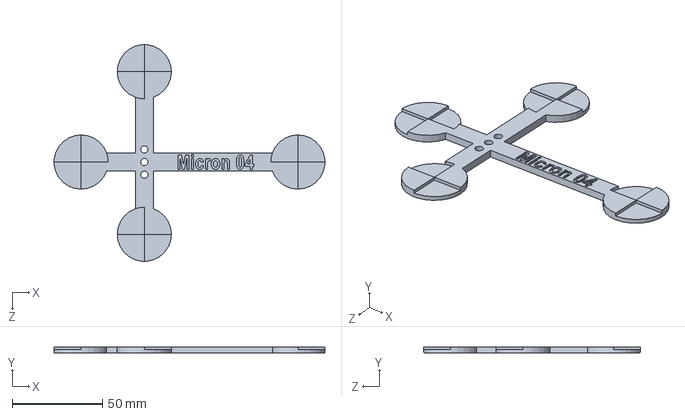
[picture p98: CAD file, 2016-07-01]
TrackingFixtures/Micron_Maker04-White.SLDPRT
150.0 x 3.50 x 120.0 mm
