PlusToolkit/PlusModelCatalog/TrackingFixtures/Micron_Black.SLDPRT

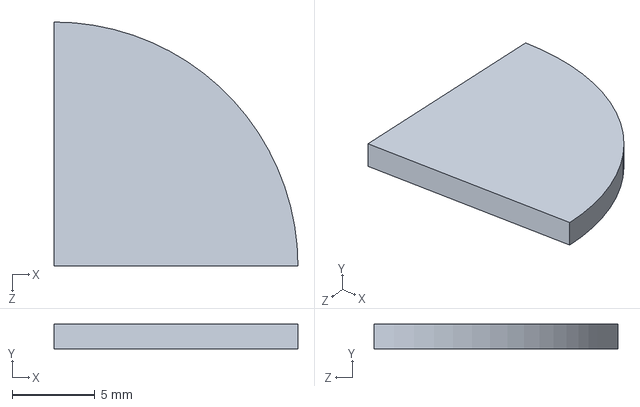
[picture p99: CAD file, 2016-06-28]
TrackingFixtures/Micron_Black.SLDPRT
14.8 x 1.50 x 14.8 mm
