PlusToolkit/PlusModelCatalog/TrackingFixtures/NeedleGrabber-BardDuaLok.SLDPRT

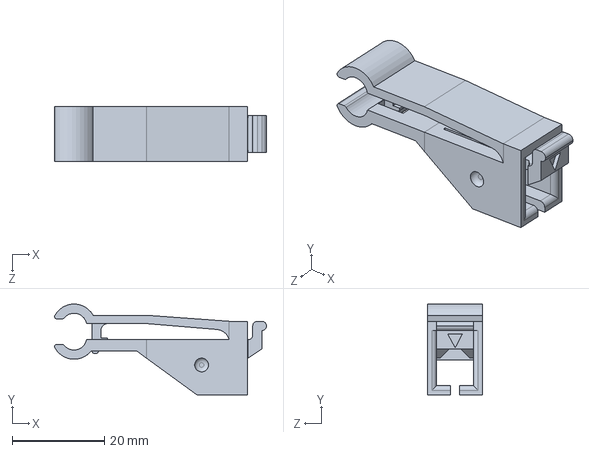
[picture p100: CAD file, 2016-05-17]
TrackingFixtures/NeedleGrabber-BardDuaLok.SLDPRT
46.1 x 19.7 x 12.0 mm
