PlusToolkit/PlusModelCatalog/TrackingFixtures/NeedleGrabber_16-20G.SLDPRT

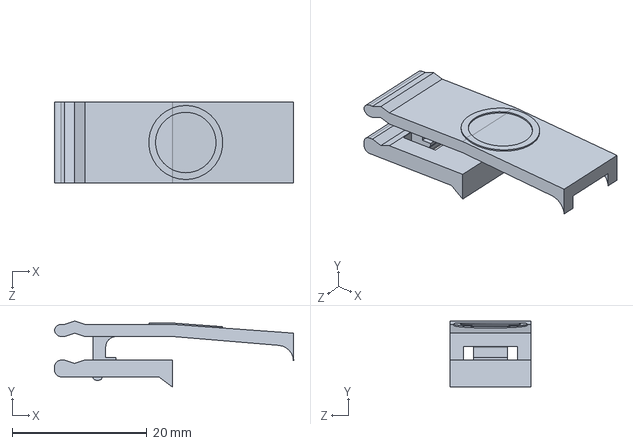
[picture p101: CAD file, 2016-04-04]
TrackingFixtures/NeedleGrabber_16-20G.SLDPRT
35.5 x 9.80 x 12.0 mm
