PlusToolkit/PlusModelCatalog/TrackingFixtures/CauteryGrabber.SLDPRT

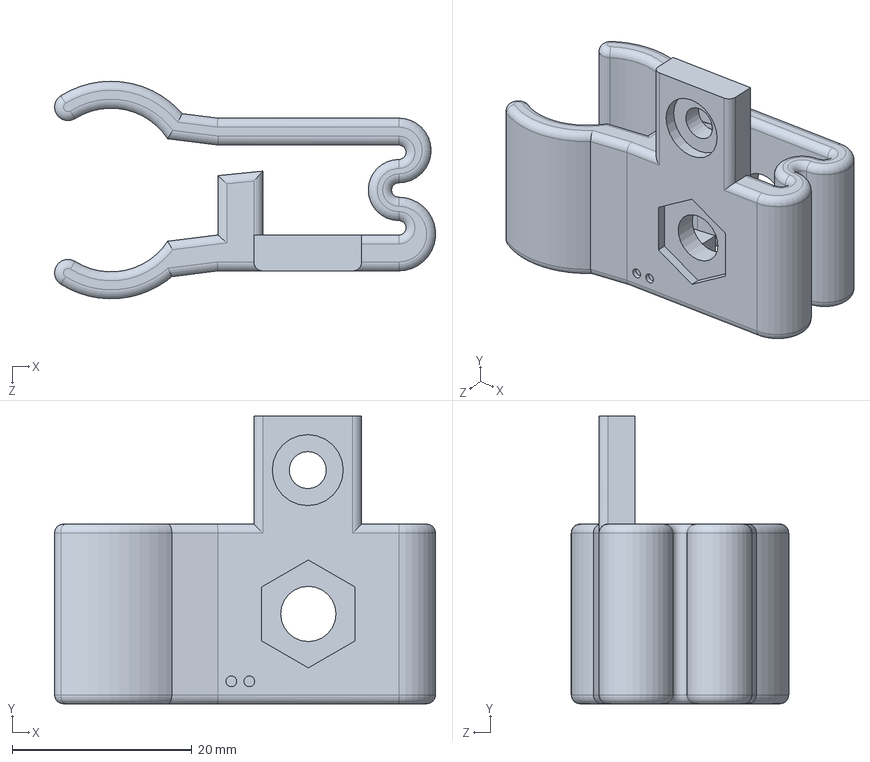
[picture p102: CAD file, 2016-01-27]
TrackingFixtures/CauteryGrabber.SLDPRT
42.4 x 32.0 x 24.2 mm
