PlusToolkit/PlusModelCatalog/TrackingFixtures/SensorHolder-OneHole.SLDPRT

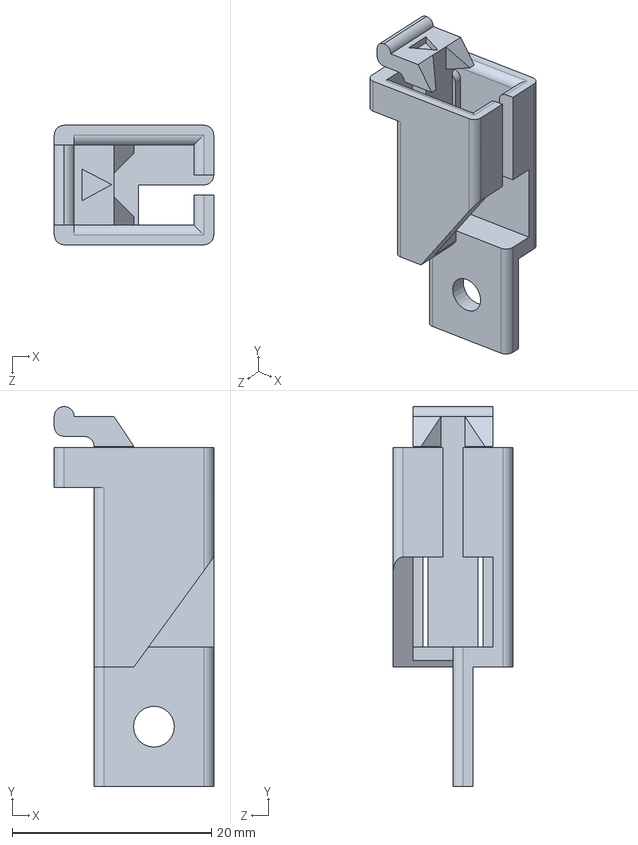
[picture p103: CAD file, 2016-01-04]
TrackingFixtures/SensorHolder-OneHole.SLDPRT
16.0 x 38.1 x 12.0 mm
