PlusToolkit/PlusModelCatalog/TrackingFixtures/OrientationLR-Plane.SLDPRT

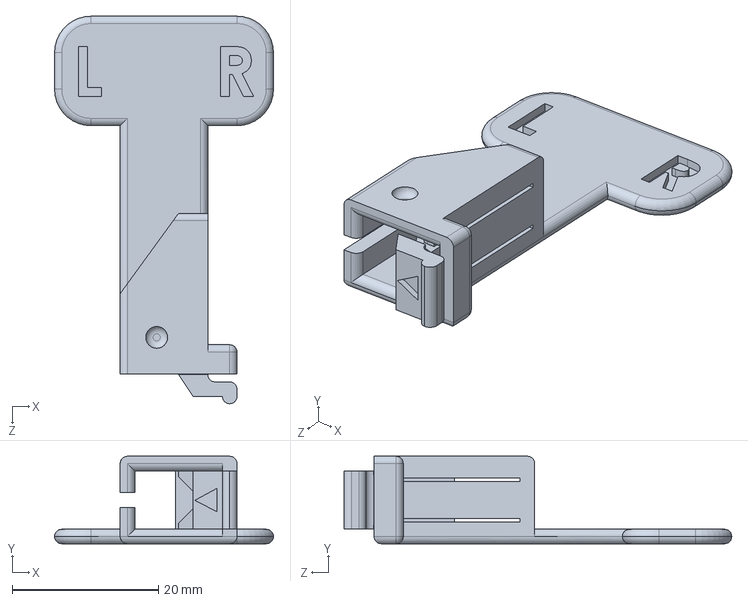
[picture p104: CAD file, 2015-12-03]
TrackingFixtures/OrientationLR-Plane.SLDPRT
30.0 x 12.0 x 53.1 mm
