PlusToolkit/PlusModelCatalog/TrackingFixtures/CandyCaneTip_100mm.SLDPRT

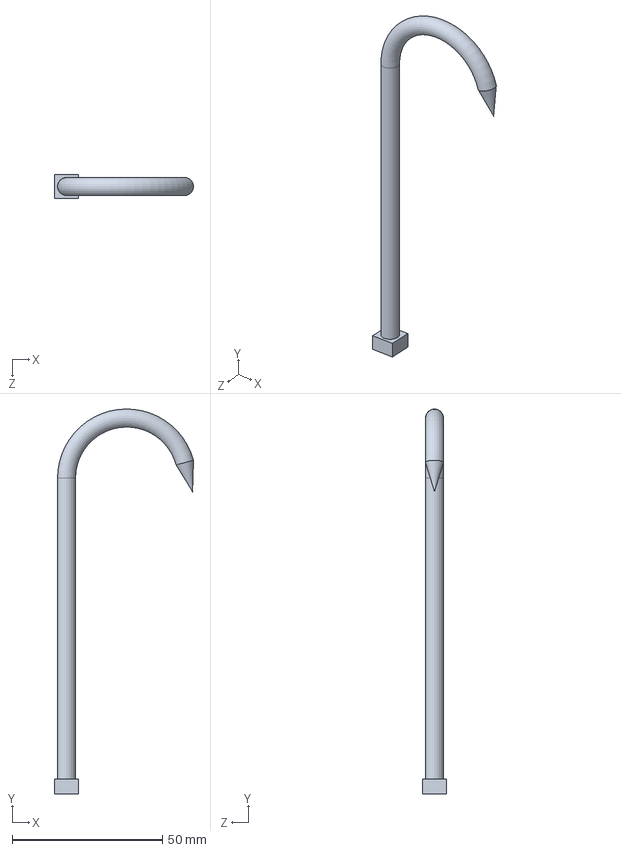
[picture p105: CAD file, 2015-09-16]
TrackingFixtures/CandyCaneTip_100mm.SLDPRT
46.2 x 128.0 x 8.00 mm
