PlusToolkit/PlusModelCatalog/TrackingFixtures/SensorHolderConnector_1.0.SLDPRT

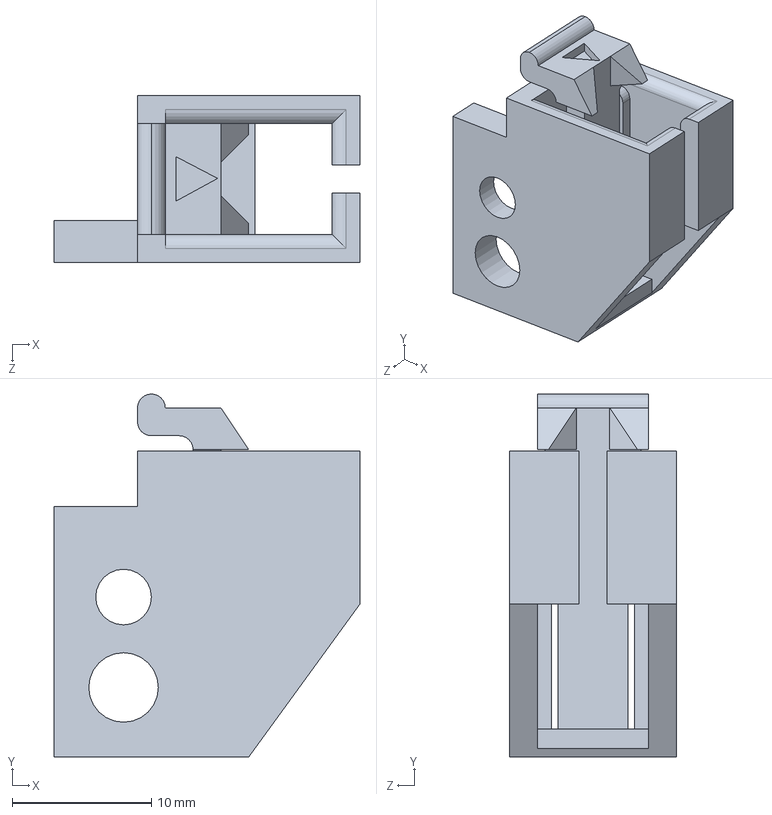
[picture p106: CAD file, 2015-06-15]
TrackingFixtures/SensorHolderConnector_1.0.SLDPRT
22.0 x 26.1 x 12.0 mm
