PlusToolkit/PlusModelCatalog/TrackingFixtures/Pointer-TwoConnectors.SLDPRT

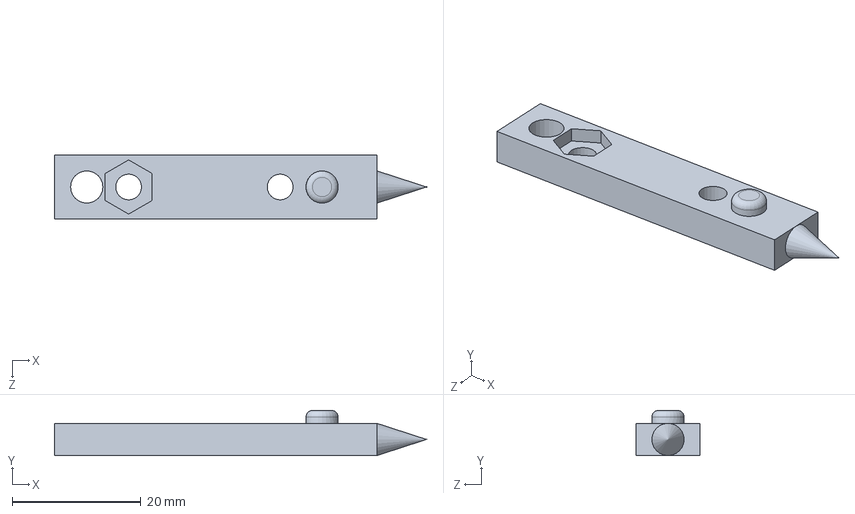
[picture p107: CAD file, 2015-06-15]
TrackingFixtures/Pointer-TwoConnectors.SLDPRT
57.7 x 7.00 x 10.0 mm
