PlusToolkit/PlusModelCatalog/TrackingFixtures/MicronPlate01.SLDPRT

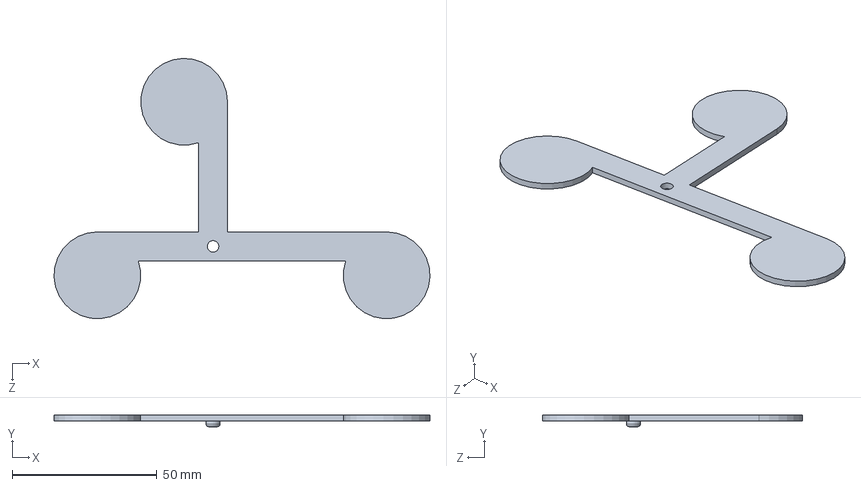
[picture p108: CAD file, 2015-06-15]
TrackingFixtures/MicronPlate01.SLDPRT
130.0 x 4.00 x 89.9 mm
