PlusToolkit/PlusModelCatalog/TrackingFixtures/PolarisAscensionPointer.SLDPRT

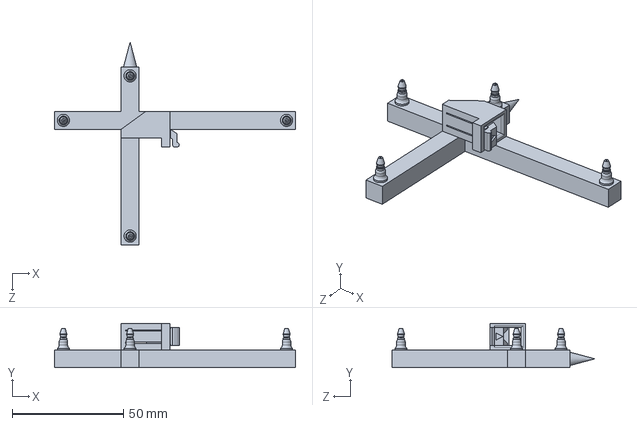
[picture p109: CAD file, 2015-06-08]
TrackingFixtures/PolarisAscensionPointer.SLDPRT
108.3 x 20.0 x 91.2 mm
