PlusToolkit/PlusModelCatalog/TrackingFixtures/PolarisMarkerBase.SLDPRT

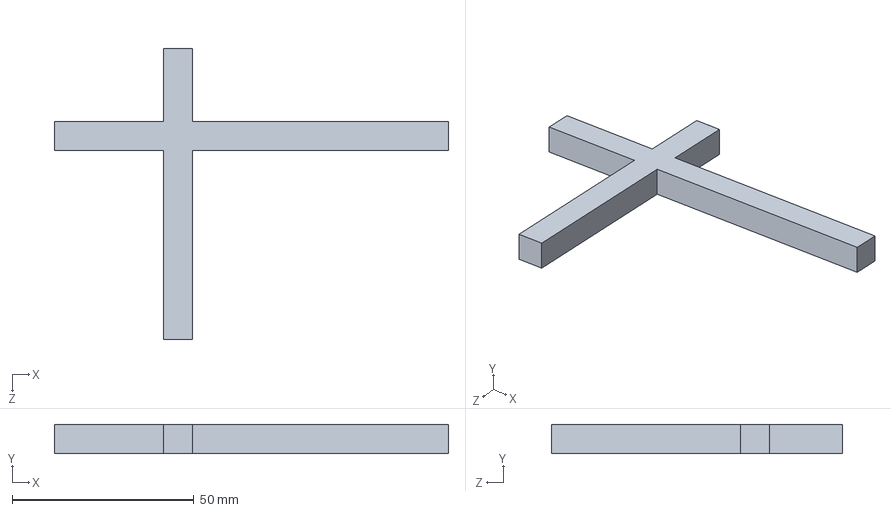
[picture p110: CAD file, 2015-05-02]
TrackingFixtures/PolarisMarkerBase.SLDPRT
108.3 x 8.00 x 80.0 mm
