PlusToolkit/PlusModelCatalog/TrackingFixtures/locneedle_1.0.SLDPRT

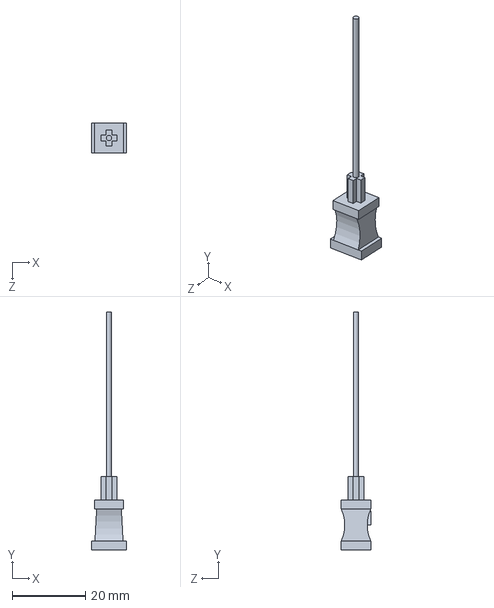
[picture p111: CAD file, 2015-01-29]
TrackingFixtures/locneedle_1.0.SLDPRT
9.70 x 65.2 x 8.10 mm
