PlusToolkit/PlusModelCatalog/TrackingFixtures/SensorHolder-Ordered_2mm_1.0.stl

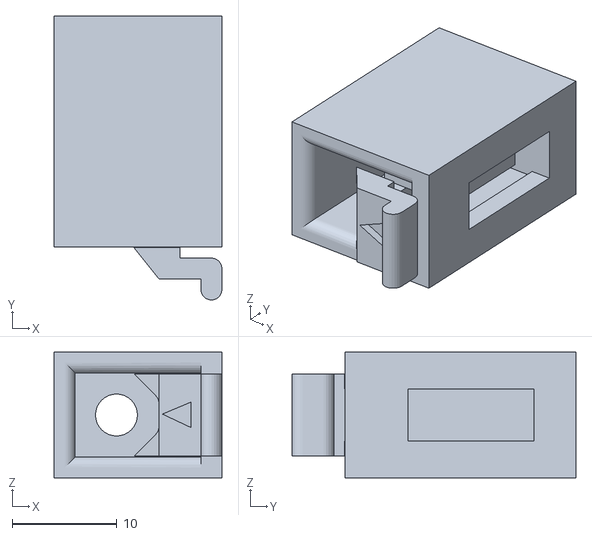
[picture p112: CAD file, 2015-01-06]
TrackingFixtures/SensorHolder-Ordered_2mm_1.0.stl
16.0 x 27.1 x 12.0
