PlusToolkit/PlusModelCatalog/TrackingFixtures/SensorHolder-Ordered-HolesInterface_2mm_1.0.stl

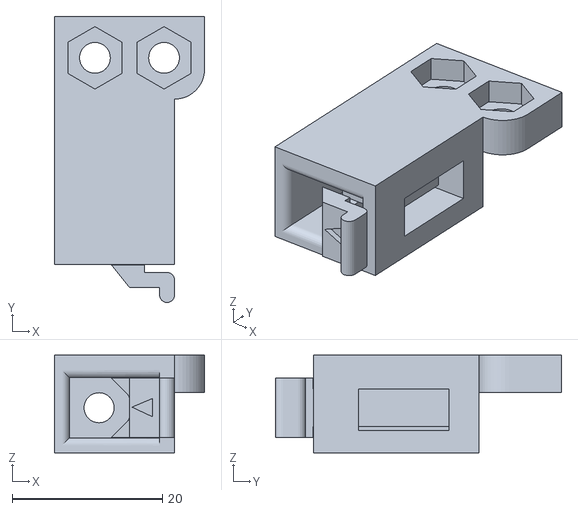
[picture p113: CAD file, 2015-01-06]
TrackingFixtures/SensorHolder-Ordered-HolesInterface_2mm_1.0.stl
20.0 x 38.1 x 13.0
