PlusToolkit/PlusModelCatalog/TrackingFixtures/SensorHolder-GlueHoles-Ordered_2mm_1.0.stl

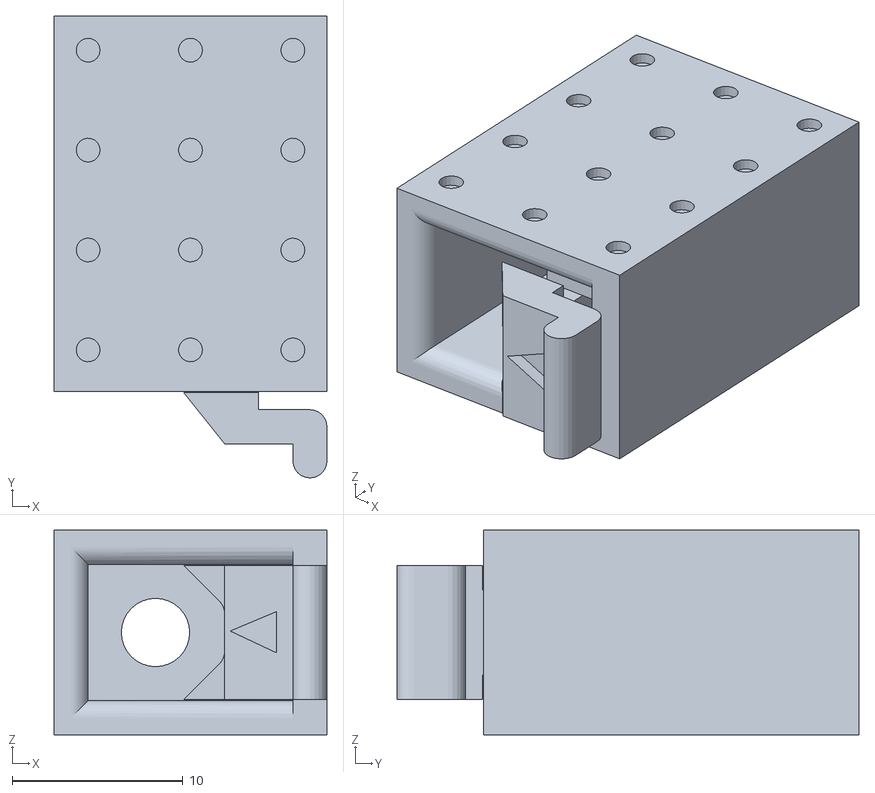
[picture p114: CAD file, 2014-11-28]
TrackingFixtures/SensorHolder-GlueHoles-Ordered_2mm_1.0.stl
16.0 x 27.1 x 12.0
