PlusToolkit/PlusModelCatalog/TrackingFixtures/Plug-L_60mm_3.0.stl

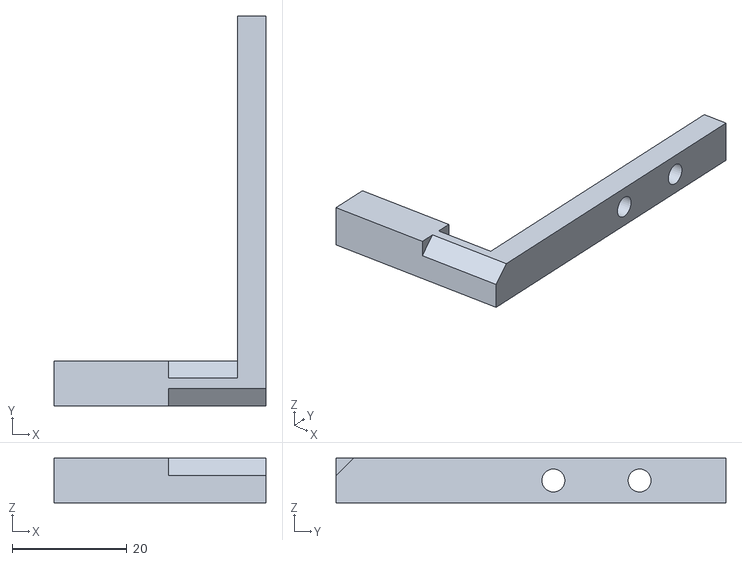
[picture p115: CAD file, 2014-11-28]
TrackingFixtures/Plug-L_60mm_3.0.stl
36.9 x 67.8 x 7.80
