PlusToolkit/PlusModelCatalog/TrackingFixtures/Concept_ScoliosisMicronTracker_2.0.stl

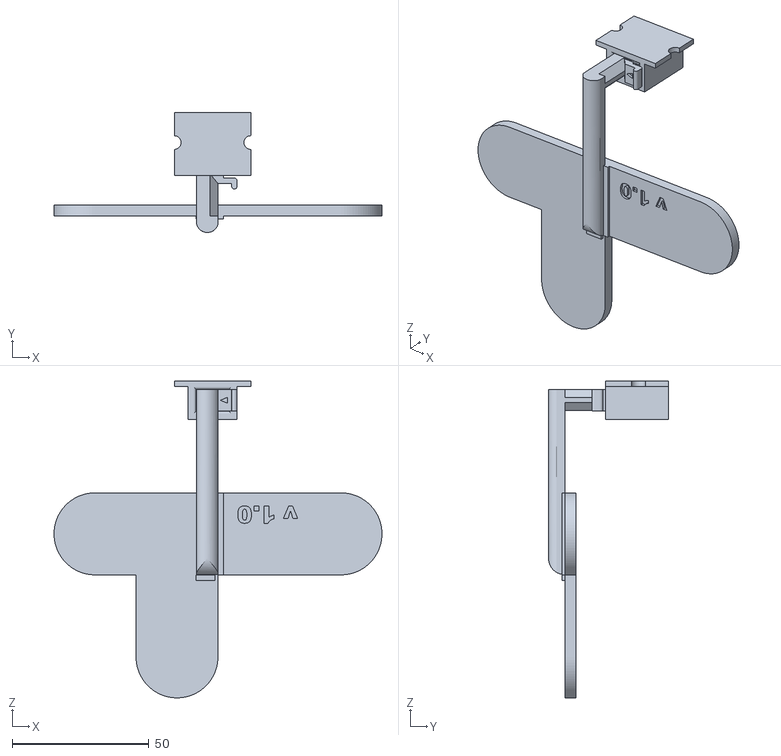
[picture p116: CAD file, 2014-11-28]
TrackingFixtures/Concept_ScoliosisMicronTracker_2.0.stl
120.0 x 43.9 x 115.9
