PlusToolkit/PlusModelCatalog/TrackingFixtures/SensorHolder_Wing_1.0.stl

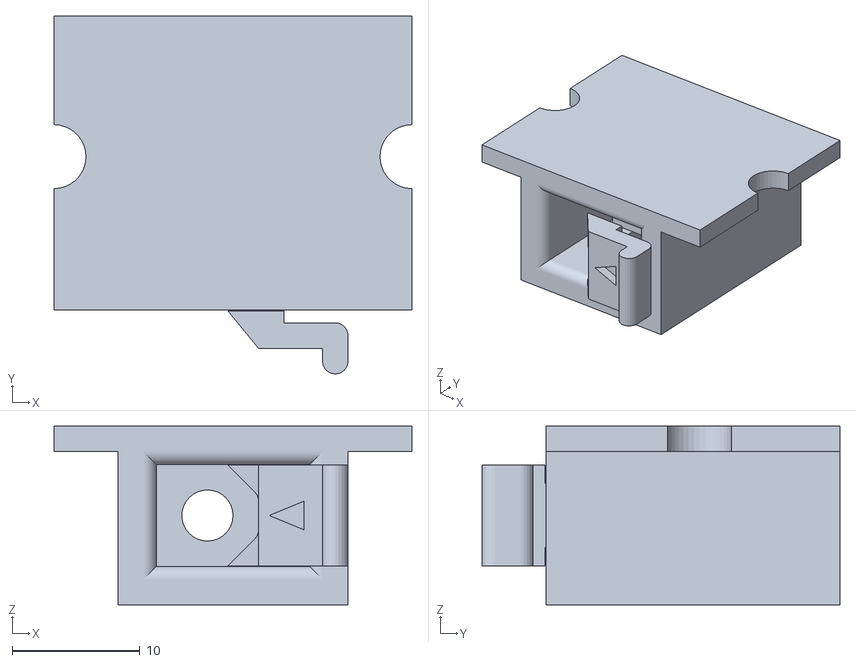
[picture p117: CAD file, 2014-11-28]
TrackingFixtures/SensorHolder_Wing_1.0.stl
28.0 x 28.0 x 14.0
