PlusToolkit/PlusModelCatalog/TrackingFixtures/Stylus_60mm.stl

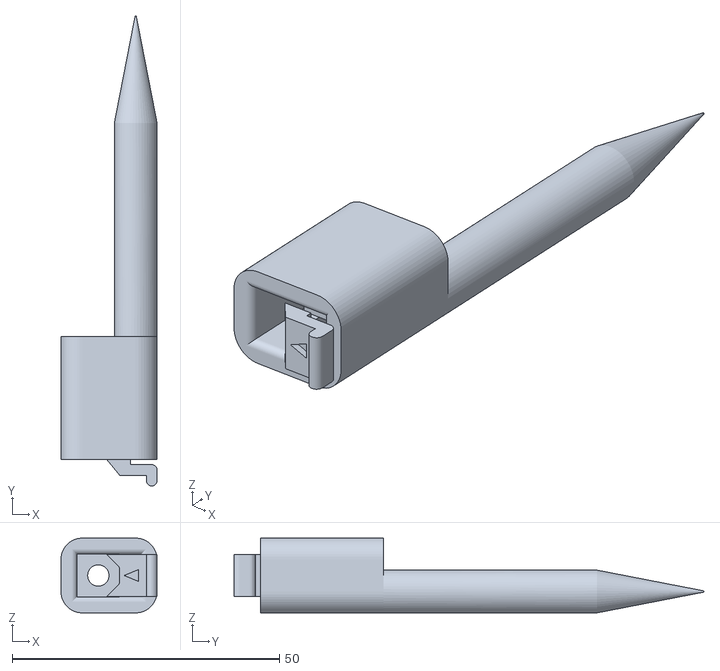
[picture p118: CAD file, 2014-11-28]
TrackingFixtures/Stylus_60mm.stl
18.0 x 88.0 x 14.0
