PlusToolkit/PlusModelCatalog/fCalPhantom/fCal_1/PhantomDefinition_fCal_1.1_Wiring_1.0.png

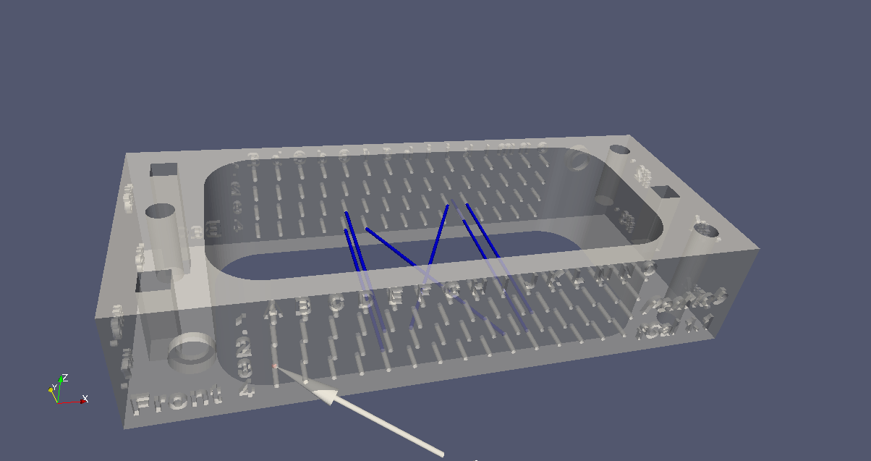
fCalPhantom/fCal_1/PhantomDefinition_fCal_1.1_Wiring_1.0.png
