PlusToolkit/PlusModelCatalog/fCalPhantom/fCal_2/PhantomDefinition_fCal_2.0_Wiring_2.0-transp.png

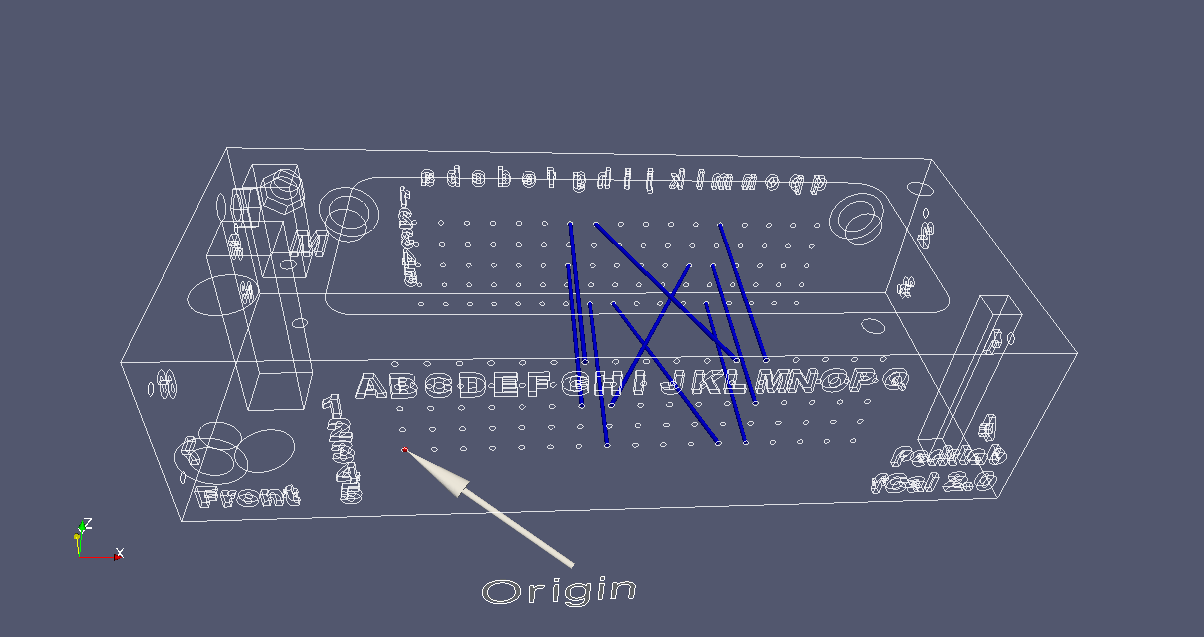
fCalPhantom/fCal_2/PhantomDefinition_fCal_2.0_Wiring_2.0-transp.png
