PlusToolkit/PlusModelCatalog/fCalPhantom/fCal_L1/BuildingInstructionManual/LPub/assem/legophantom1_1_0_0_0_1_0_0_0_1_4_1275_150_DPCM_1.png

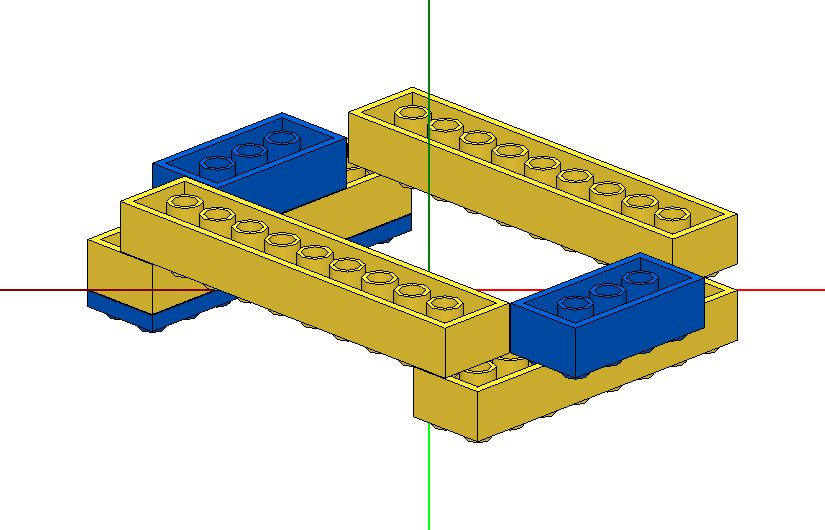
fCalPhantom/fCal_L1/BuildingInstructionManual/LPub/assem/legophantom1_1_0_0_0_1_0_0_0_1_4_1275_150_DPCM_1.png
