PlusToolkit/PlusModelCatalog/fCalPhantom/fCal_L1/BuildingInstructionManual/Pictures/middleNWire_above.png

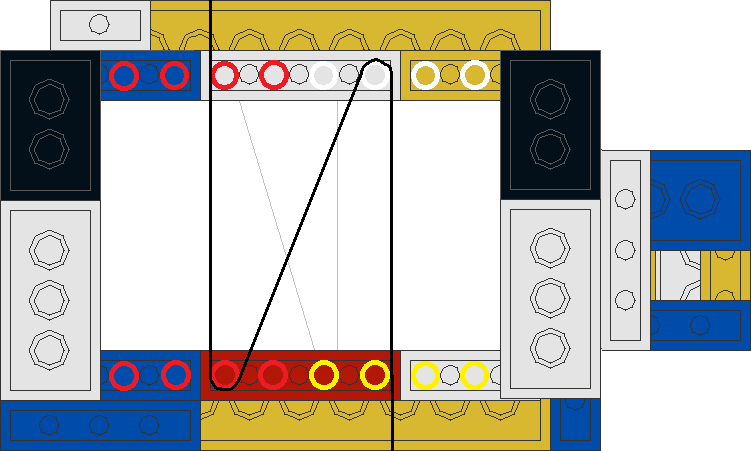
fCalPhantom/fCal_L1/BuildingInstructionManual/Pictures/middleNWire_above.png
