PlusToolkit/PlusModelCatalog/fCalPhantom/fCal_L1/BuildingInstructionManual/Pictures/middleNWire_iso.png

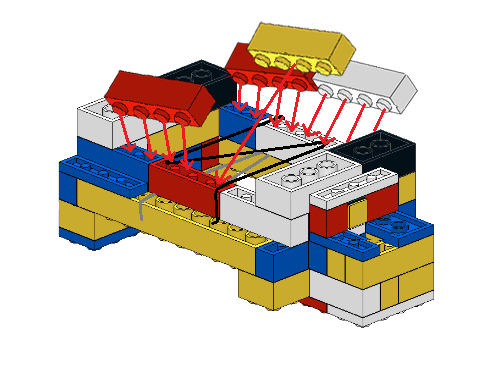
fCalPhantom/fCal_L1/BuildingInstructionManual/Pictures/middleNWire_iso.png
