PlusToolkit/PlusModelCatalog/TrackingFixtures/MC10_ProbeHolder/MC10_ProbeHolder_AssemblyPhoto1.JPG

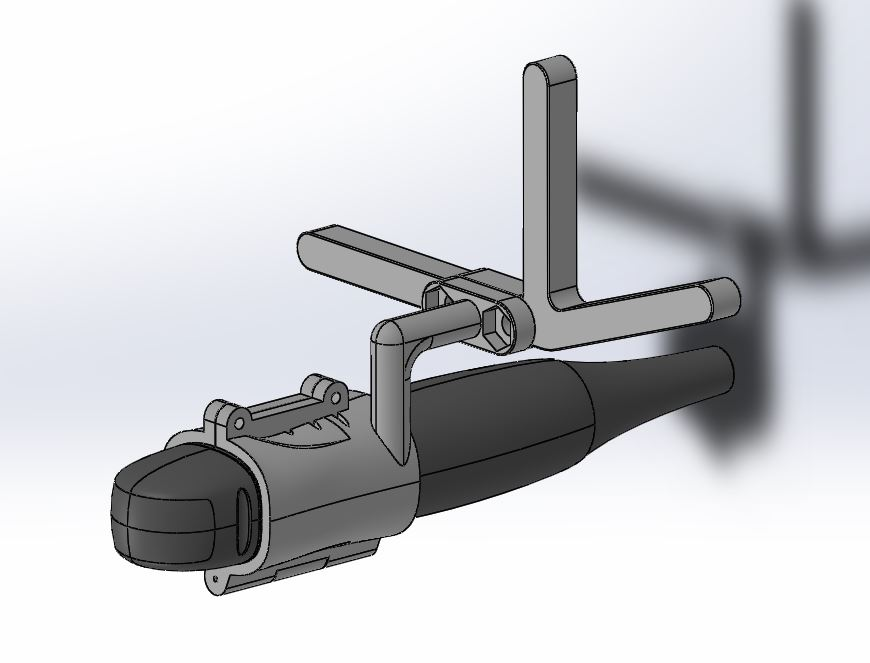
TrackingFixtures/MC10_ProbeHolder/MC10_ProbeHolder_AssemblyPhoto1.JPG
