PlusToolkit/PlusModelCatalog/TrackingFixtures/NeedleClip-Assembly_16-20G.png

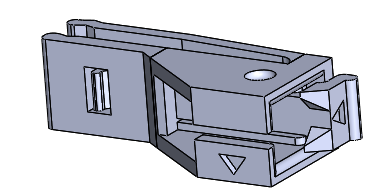
TrackingFixtures/NeedleClip-Assembly_16-20G.png
